Blizzard26/OAM-KNX2HovalGateway/include/knxprod.h

#pragma once


#define paramDelay(time) (uint32_t)( \
            (time & 0xC000) == 0xC000 ? (time & 0x3FFF) * 100 : \
            (time & 0xC000) == 0x0000 ? (time & 0x3FFF) * 1000 : \
            (time & 0xC000) == 0x4000 ? (time & 0x3FFF) * 60000 : \
            (time & 0xC000) == 0x8000 ? ((time & 0x3FFF) > 1000 ? 3600000 : \
                                         (time & 0x3FFF) * 3600000 ) : 0 )
                                             
#define ETS_ModuleId_NONE 0
#define ETS_ModuleId_BASE 1
#define ETS_ModuleId_UCT 2
#define ETS_ModuleId_HOV 3
#define ETS_ModuleId_LOG 4
#define MAIN_FirmwareName "KNX-Hoval Gateway"
#define MAIN_OpenKnxId 0xFF
#define MAIN_ApplicationNumber 26
#define MAIN_ApplicationVersion 4
#define MAIN_FirmwareRevision 0
#define MAIN_ApplicationEncoding iso-8859-15
#define MAIN_ParameterSize 4949
#define MAIN_MaxKoNumber 1059
#define MAIN_OrderNumber "AL-OpenKnxHovalGateway"
#define BASE_ModuleVersion 23
#define UCT_ModuleVersion 5
#define HOV_ModuleVersion 4
#define LOG_ModuleVersion 64
// Parameter with single occurrence


#define BASE_StartupDelayBase                     0      // 2 Bits, Bit 7-6
#define     BASE_StartupDelayBaseMask 0xC0
#define     BASE_StartupDelayBaseShift 6
#define BASE_StartupDelayTime                     0      // 14 Bits, Bit 13-0
#define     BASE_StartupDelayTimeMask 0x3FFF
#define     BASE_StartupDelayTimeShift 0
#define BASE_HeartbeatDelayBase                   2      // 2 Bits, Bit 7-6
#define     BASE_HeartbeatDelayBaseMask 0xC0
#define     BASE_HeartbeatDelayBaseShift 6
#define BASE_HeartbeatDelayTime                   2      // 14 Bits, Bit 13-0
#define     BASE_HeartbeatDelayTimeMask 0x3FFF
#define     BASE_HeartbeatDelayTimeShift 0
#define BASE_Timezone                             4      // 5 Bits, Bit 7-3
#define     BASE_TimezoneMask 0xF8
#define     BASE_TimezoneShift 3
#define BASE_CombinedTimeDate                     4      // 1 Bit, Bit 2
#define     BASE_CombinedTimeDateMask 0x04
#define     BASE_CombinedTimeDateShift 2
#define BASE_SummertimeAll                        4      // 2 Bits, Bit 1-0
#define     BASE_SummertimeAllMask 0x03
#define     BASE_SummertimeAllShift 0
#define BASE_SummertimeDE                         4      // 2 Bits, Bit 1-0
#define     BASE_SummertimeDEMask 0x03
#define     BASE_SummertimeDEShift 0
#define BASE_SummertimeWorld                      4      // 2 Bits, Bit 1-0
#define     BASE_SummertimeWorldMask 0x03
#define     BASE_SummertimeWorldShift 0
#define BASE_SummertimeKO                         4      // 2 Bits, Bit 1-0
#define     BASE_SummertimeKOMask 0x03
#define     BASE_SummertimeKOShift 0
#define BASE_TimezoneCustom                       5      // char*, 63 Byte
#define     BASE_TimezoneCustomLength 63
#define BASE_Latitude                            69      // float (4 Byte)
#define BASE_Longitude                           73      // float (4 Byte)
#define BASE_Diagnose                            78      // 1 Bit, Bit 7
#define     BASE_DiagnoseMask 0x80
#define     BASE_DiagnoseShift 7
#define BASE_Watchdog                            78      // 1 Bit, Bit 6
#define     BASE_WatchdogMask 0x40
#define     BASE_WatchdogShift 6
#define BASE_ReadTimeDate                        78      // 1 Bit, Bit 5
#define     BASE_ReadTimeDateMask 0x20
#define     BASE_ReadTimeDateShift 5
#define BASE_HeartbeatExtended                   78      // 1 Bit, Bit 4
#define     BASE_HeartbeatExtendedMask 0x10
#define     BASE_HeartbeatExtendedShift 4
#define BASE_InternalTime                        78      // 1 Bit, Bit 3
#define     BASE_InternalTimeMask 0x08
#define     BASE_InternalTimeShift 3
#define BASE_ManualSave                          78      // 3 Bits, Bit 2-0
#define     BASE_ManualSaveMask 0x07
#define     BASE_ManualSaveShift 0
#define BASE_PeriodicSave                        79      // 8 Bits, Bit 7-0
#define BASE_Info1LedFunc                        80      // 16 Bits, Bit 15-0
#define BASE_Info2LedFunc                        82      // 16 Bits, Bit 15-0
#define BASE_Info3LedFunc                        84      // 16 Bits, Bit 15-0
#define BASE_DefaultLedFunc                      86      // 1 Bit, Bit 7
#define     BASE_DefaultLedFuncMask 0x80
#define     BASE_DefaultLedFuncShift 7
#define BASE_Dummy                               109      // uint8_t
#define BASE_ModuleEnabled_UCT                   110      // 1 Bit, Bit 6
#define     BASE_ModuleEnabled_UCTMask 0x40
#define     BASE_ModuleEnabled_UCTShift 6
#define BASE_ModuleEnabled_HOV                   110      // 1 Bit, Bit 5
#define     BASE_ModuleEnabled_HOVMask 0x20
#define     BASE_ModuleEnabled_HOVShift 5
#define BASE_ModuleEnabled_LOG                   110      // 1 Bit, Bit 4
#define     BASE_ModuleEnabled_LOGMask 0x10
#define     BASE_ModuleEnabled_LOGShift 4

// Zeitbasis
#define ParamBASE_StartupDelayBase                    ((knx.paramByte(BASE_StartupDelayBase) & BASE_StartupDelayBaseMask) >> BASE_StartupDelayBaseShift)
// Zeit
#define ParamBASE_StartupDelayTime                    (knx.paramWord(BASE_StartupDelayTime) & BASE_StartupDelayTimeMask)
// Zeit (in Millisekunden)
#define ParamBASE_StartupDelayTimeMS                  (paramDelay(knx.paramWord(BASE_StartupDelayTime)))
// Zeitbasis
#define ParamBASE_HeartbeatDelayBase                  ((knx.paramByte(BASE_HeartbeatDelayBase) & BASE_HeartbeatDelayBaseMask) >> BASE_HeartbeatDelayBaseShift)
// Zeit
#define ParamBASE_HeartbeatDelayTime                  (knx.paramWord(BASE_HeartbeatDelayTime) & BASE_HeartbeatDelayTimeMask)
// Zeit (in Millisekunden)
#define ParamBASE_HeartbeatDelayTimeMS                (paramDelay(knx.paramWord(BASE_HeartbeatDelayTime)))
// Zeitzone
#define ParamBASE_Timezone                            ((knx.paramByte(BASE_Timezone) & BASE_TimezoneMask) >> BASE_TimezoneShift)
// Empfangen über
#define ParamBASE_CombinedTimeDate                    ((bool)(knx.paramByte(BASE_CombinedTimeDate) & BASE_CombinedTimeDateMask))
// Sommerzeit ermitteln durch
#define ParamBASE_SummertimeAll                       (knx.paramByte(BASE_SummertimeAll) & BASE_SummertimeAllMask)
// Sommerzeit ermitteln durch
#define ParamBASE_SummertimeDE                        (knx.paramByte(BASE_SummertimeDE) & BASE_SummertimeDEMask)
// Sommerzeit ermitteln durch
#define ParamBASE_SummertimeWorld                     (knx.paramByte(BASE_SummertimeWorld) & BASE_SummertimeWorldMask)
// Sommerzeit ermitteln durch
#define ParamBASE_SummertimeKO                        (knx.paramByte(BASE_SummertimeKO) & BASE_SummertimeKOMask)
// POSIX TZ-String
#define ParamBASE_TimezoneCustom                      (knx.paramData(BASE_TimezoneCustom))
#define ParamBASE_TimezoneCustomStr                   (knx.paramString(BASE_TimezoneCustom, BASE_TimezoneCustomLength))
// Breitengrad
#define ParamBASE_Latitude                            (knx.paramFloat(BASE_Latitude, Float_Enc_IEEE754Single))
// Längengrad
#define ParamBASE_Longitude                           (knx.paramFloat(BASE_Longitude, Float_Enc_IEEE754Single))
// Diagnoseobjekt anzeigen
#define ParamBASE_Diagnose                            ((bool)(knx.paramByte(BASE_Diagnose) & BASE_DiagnoseMask))
// Watchdog aktivieren
#define ParamBASE_Watchdog                            ((bool)(knx.paramByte(BASE_Watchdog) & BASE_WatchdogMask))
// Bei Neustart vom Bus lesen
#define ParamBASE_ReadTimeDate                        ((bool)(knx.paramByte(BASE_ReadTimeDate) & BASE_ReadTimeDateMask))
// Erweitertes "In Betrieb"
#define ParamBASE_HeartbeatExtended                   ((bool)(knx.paramByte(BASE_HeartbeatExtended) & BASE_HeartbeatExtendedMask))
// InternalTime
#define ParamBASE_InternalTime                        ((bool)(knx.paramByte(BASE_InternalTime) & BASE_InternalTimeMask))
// Manuelles speichern
#define ParamBASE_ManualSave                          (knx.paramByte(BASE_ManualSave) & BASE_ManualSaveMask)
// Zyklisches speichern
#define ParamBASE_PeriodicSave                        (knx.paramByte(BASE_PeriodicSave))
// Info1
#define ParamBASE_Info1LedFunc                        (knx.paramWord(BASE_Info1LedFunc))
// Info2
#define ParamBASE_Info2LedFunc                        (knx.paramWord(BASE_Info2LedFunc))
// Info3
#define ParamBASE_Info3LedFunc                        (knx.paramWord(BASE_Info3LedFunc))
// 
#define ParamBASE_DefaultLedFunc                      ((bool)(knx.paramByte(BASE_DefaultLedFunc) & BASE_DefaultLedFuncMask))
// 
#define ParamBASE_Dummy                               (knx.paramByte(BASE_Dummy))
// UCT
#define ParamBASE_ModuleEnabled_UCT                   ((bool)(knx.paramByte(BASE_ModuleEnabled_UCT) & BASE_ModuleEnabled_UCTMask))
// HOV
#define ParamBASE_ModuleEnabled_HOV                   ((bool)(knx.paramByte(BASE_ModuleEnabled_HOV) & BASE_ModuleEnabled_HOVMask))
// LOG
#define ParamBASE_ModuleEnabled_LOG                   ((bool)(knx.paramByte(BASE_ModuleEnabled_LOG) & BASE_ModuleEnabled_LOGMask))

#define BASE_KoHeartbeat 1
#define BASE_KoTime 2
#define BASE_KoDate 3
#define BASE_KoDateTime 4
#define BASE_KoIsSummertime 5
#define BASE_KoManualSave 6
#define BASE_KoDiagnose 7

// In Betrieb
#define KoBASE_Heartbeat                           (knx.getGroupObject(BASE_KoHeartbeat))
// Uhrzeit
#define KoBASE_Time                                (knx.getGroupObject(BASE_KoTime))
// Datum
#define KoBASE_Date                                (knx.getGroupObject(BASE_KoDate))
// Uhrzeit/Datum
#define KoBASE_DateTime                            (knx.getGroupObject(BASE_KoDateTime))
// Sommerzeit aktiv
#define KoBASE_IsSummertime                        (knx.getGroupObject(BASE_KoIsSummertime))
// Speichern
#define KoBASE_ManualSave                          (knx.getGroupObject(BASE_KoManualSave))
// Diagnose
#define KoBASE_Diagnose                            (knx.getGroupObject(BASE_KoDiagnose))



#define HOV_GatewayDeviceType                   114      // uint8_t
#define HOV_GatewayDeviceId                     115      // uint8_t
#define HOV_GeneralExpertMode                   116      // 1 Bit, Bit 7
#define     HOV_GeneralExpertModeMask 0x80
#define     HOV_GeneralExpertModeShift 7
#define HOV_HVDeviceType                        122      // uint8_t
#define HOV_HVDeviceId                          123      // uint8_t
#define HOV_HVSendActiveDelayBase               124      // 2 Bits, Bit 7-6
#define     HOV_HVSendActiveDelayBaseMask 0xC0
#define     HOV_HVSendActiveDelayBaseShift 6
#define HOV_HVSendActiveDelayTime               124      // 14 Bits, Bit 13-0
#define     HOV_HVSendActiveDelayTimeMask 0x3FFF
#define     HOV_HVSendActiveDelayTimeShift 0
#define HOV_HVVocSensorPresent                  126      // 1 Bit, Bit 7
#define     HOV_HVVocSensorPresentMask 0x80
#define     HOV_HVVocSensorPresentShift 7
#define HOV_GeneralRpm2Present                  126      // 1 Bit, Bit 6
#define     HOV_GeneralRpm2PresentMask 0x40
#define     HOV_GeneralRpm2PresentShift 6
#define HOV_HVPollingIntervalDelayBase          127      // 2 Bits, Bit 7-6
#define     HOV_HVPollingIntervalDelayBaseMask 0xC0
#define     HOV_HVPollingIntervalDelayBaseShift 6
#define HOV_HVPollingIntervalDelayTime          127      // 14 Bits, Bit 13-0
#define     HOV_HVPollingIntervalDelayTimeMask 0x3FFF
#define     HOV_HVPollingIntervalDelayTimeShift 0
#define HOV_HVSendEveryChange                   128      // 1 Bit, Bit 7
#define     HOV_HVSendEveryChangeMask 0x80
#define     HOV_HVSendEveryChangeShift 7
#define HOV_HVsendIntervalDelayBase             129      // 2 Bits, Bit 7-6
#define     HOV_HVsendIntervalDelayBaseMask 0xC0
#define     HOV_HVsendIntervalDelayBaseShift 6
#define HOV_HVSendIntervalDelayTime             129      // 14 Bits, Bit 13-0
#define     HOV_HVSendIntervalDelayTimeMask 0x3FFF
#define     HOV_HVSendIntervalDelayTimeShift 0
#define HOV_dummy                               138      // 1 Bit, Bit 7
#define     HOV_dummyMask 0x80
#define     HOV_dummyShift 7

// Gateway Typ (wird verwendet für Anfragen an die Lüftung; Typisch 64)
#define ParamHOV_GatewayDeviceType                   (knx.paramByte(HOV_GatewayDeviceType))
// Gateway Id (wird verwendet für Anfragen an die Lüftung; Typisch 8 oder 9)
#define ParamHOV_GatewayDeviceId                     (knx.paramByte(HOV_GatewayDeviceId))
// Expertenmodus
#define ParamHOV_GeneralExpertMode                   ((bool)(knx.paramByte(HOV_GeneralExpertMode) & HOV_GeneralExpertModeMask))
// Typ (HomeVent: 32)
#define ParamHOV_HVDeviceType                        (knx.paramByte(HOV_HVDeviceType))
// Addresse (Typisch 8)
#define ParamHOV_HVDeviceId                          (knx.paramByte(HOV_HVDeviceId))
// Zeitbasis
#define ParamHOV_HVSendActiveDelayBase               ((knx.paramByte(HOV_HVSendActiveDelayBase) & HOV_HVSendActiveDelayBaseMask) >> HOV_HVSendActiveDelayBaseShift)
// Zeit
#define ParamHOV_HVSendActiveDelayTime               (knx.paramWord(HOV_HVSendActiveDelayTime) & HOV_HVSendActiveDelayTimeMask)
// Zeit (in Millisekunden)
#define ParamHOV_HVSendActiveDelayTimeMS             (paramDelay(knx.paramWord(HOV_HVSendActiveDelayTime)))
// VOC Sensor vorhanden
#define ParamHOV_HVVocSensorPresent                  ((bool)(knx.paramByte(HOV_HVVocSensorPresent) & HOV_HVVocSensorPresentMask))
// RPM2 Present
#define ParamHOV_GeneralRpm2Present                  ((bool)(knx.paramByte(HOV_GeneralRpm2Present) & HOV_GeneralRpm2PresentMask))
// Zeitbasis
#define ParamHOV_HVPollingIntervalDelayBase          ((knx.paramByte(HOV_HVPollingIntervalDelayBase) & HOV_HVPollingIntervalDelayBaseMask) >> HOV_HVPollingIntervalDelayBaseShift)
// Zeit
#define ParamHOV_HVPollingIntervalDelayTime          (knx.paramWord(HOV_HVPollingIntervalDelayTime) & HOV_HVPollingIntervalDelayTimeMask)
// Zeit (in Millisekunden)
#define ParamHOV_HVPollingIntervalDelayTimeMS        (paramDelay(knx.paramWord(HOV_HVPollingIntervalDelayTime)))
// Jede Änderung senden
#define ParamHOV_HVSendEveryChange                   ((bool)(knx.paramByte(HOV_HVSendEveryChange) & HOV_HVSendEveryChangeMask))
// Zeitbasis
#define ParamHOV_HVsendIntervalDelayBase             ((knx.paramByte(HOV_HVsendIntervalDelayBase) & HOV_HVsendIntervalDelayBaseMask) >> HOV_HVsendIntervalDelayBaseShift)
// Zeit
#define ParamHOV_HVSendIntervalDelayTime             (knx.paramWord(HOV_HVSendIntervalDelayTime) & HOV_HVSendIntervalDelayTimeMask)
// Zeit (in Millisekunden)
#define ParamHOV_HVSendIntervalDelayTimeMS           (paramDelay(knx.paramWord(HOV_HVSendIntervalDelayTime)))
// Dummy
#define ParamHOV_dummy                               ((bool)(knx.paramByte(HOV_dummy) & HOV_dummyMask))

#define HOV_Koglobal_online 100
#define HOV_Kogeneral_diagnose 103
#define HOV_Kogeneral_maintenance_remaining 109
#define HOV_Kovent_operating_mode_standby 110
#define HOV_Kovent_operating_mode_week1 111
#define HOV_Kovent_operating_mode_week2 112
#define HOV_Kovent_operating_mode_constant 113
#define HOV_Kovent_operating_mode_economy 114
#define HOV_Kovent_operating_mode 119
#define HOV_Kovent_airqualitycontrol_standby 120
#define HOV_Kovent_airqualitycontrol_normal 121
#define HOV_Kovent_airqualitycontrol_voc 122
#define HOV_Kovent_airqualitycontrol_humidity 123
#define HOV_Kovent_airqualitycontrol_antifreeze 124
#define HOV_Kovent_airqualitycontrol_coolvent 125
#define HOV_Kovent_airqualitycontrol_error 126
#define HOV_Kovent_airqualitycontrol 129
#define HOV_Kovent_ventilation_control_status 139
#define HOV_Kovent_modulation 140
#define HOV_Kovent_normal_modulation 141
#define HOV_Kovent_economy_modulation 142
#define HOV_Kovent_party_mode 150
#define HOV_Kovent_pause_mode 151
#define HOV_Kovent_party_value 152
#define HOV_Kovent_pause_value 153
#define HOV_Kovent_humidity_setpoint 160
#define HOV_Kovent_humidity_exhaust 162
#define HOV_Kovent_temperature_outdoor 164
#define HOV_Kovent_temperature_exhaust 165
#define HOV_Kovent_voc_outdoor 167
#define HOV_Kovent_voc_exhaust 168
#define HOV_Kovent_ventilation_exhaust 170
#define HOV_Kogeneral_ventilator_outdoor_pwm 171
#define HOV_Kogeneral_ventilator_exhaust_pwm 172
#define HOV_Kogeneral_rpm_rotor1 173
#define HOV_Kogeneral_rpm_rotor2 174
#define HOV_Kogeneral_active_error 190
#define HOV_Kogeneral_active_error_1 191
#define HOV_Kogeneral_active_error_2 192
#define HOV_Kogeneral_active_error_3 193
#define HOV_Kogeneral_active_error_4 194
#define HOV_Kogeneral_active_error_5 195
#define HOV_Kogeneral_active_error_error 196
#define HOV_Kogeneral_active_error_warning 197

// Allgemein
#define KoHOV_global_online                       (knx.getGroupObject(HOV_Koglobal_online))
// Allgemein
#define KoHOV_general_diagnose                    (knx.getGroupObject(HOV_Kogeneral_diagnose))
// Allgemein
#define KoHOV_general_maintenance_remaining       (knx.getGroupObject(HOV_Kogeneral_maintenance_remaining))
// Betriebswahl Lüftung
#define KoHOV_vent_operating_mode_standby         (knx.getGroupObject(HOV_Kovent_operating_mode_standby))
// Betriebswahl Lüftung
#define KoHOV_vent_operating_mode_week1           (knx.getGroupObject(HOV_Kovent_operating_mode_week1))
// Betriebswahl Lüftung
#define KoHOV_vent_operating_mode_week2           (knx.getGroupObject(HOV_Kovent_operating_mode_week2))
// Betriebswahl Lüftung
#define KoHOV_vent_operating_mode_constant        (knx.getGroupObject(HOV_Kovent_operating_mode_constant))
// Betriebswahl Lüftung
#define KoHOV_vent_operating_mode_economy         (knx.getGroupObject(HOV_Kovent_operating_mode_economy))
// Betriebswahl Lüftung
#define KoHOV_vent_operating_mode                 (knx.getGroupObject(HOV_Kovent_operating_mode))
// Lüftungsregelung
#define KoHOV_vent_airqualitycontrol_standby      (knx.getGroupObject(HOV_Kovent_airqualitycontrol_standby))
// Lüftungsregelung
#define KoHOV_vent_airqualitycontrol_normal       (knx.getGroupObject(HOV_Kovent_airqualitycontrol_normal))
// Lüftungsregelung
#define KoHOV_vent_airqualitycontrol_voc          (knx.getGroupObject(HOV_Kovent_airqualitycontrol_voc))
// Lüftungsregelung
#define KoHOV_vent_airqualitycontrol_humidity     (knx.getGroupObject(HOV_Kovent_airqualitycontrol_humidity))
// Lüftungsregelung
#define KoHOV_vent_airqualitycontrol_antifreeze   (knx.getGroupObject(HOV_Kovent_airqualitycontrol_antifreeze))
// Lüftungsregelung
#define KoHOV_vent_airqualitycontrol_coolvent     (knx.getGroupObject(HOV_Kovent_airqualitycontrol_coolvent))
// Lüftungsregelung
#define KoHOV_vent_airqualitycontrol_error        (knx.getGroupObject(HOV_Kovent_airqualitycontrol_error))
// Lüftungsregelung
#define KoHOV_vent_airqualitycontrol              (knx.getGroupObject(HOV_Kovent_airqualitycontrol))
// Lüftung
#define KoHOV_vent_ventilation_control_status     (knx.getGroupObject(HOV_Kovent_ventilation_control_status))
// Lüftungsmodulation
#define KoHOV_vent_modulation                     (knx.getGroupObject(HOV_Kovent_modulation))
// Lüftungsmodulation
#define KoHOV_vent_normal_modulation              (knx.getGroupObject(HOV_Kovent_normal_modulation))
// Lüftungsmodulation
#define KoHOV_vent_economy_modulation             (knx.getGroupObject(HOV_Kovent_economy_modulation))
// Party/Pause
#define KoHOV_vent_party_mode                     (knx.getGroupObject(HOV_Kovent_party_mode))
// Party/Pause
#define KoHOV_vent_pause_mode                     (knx.getGroupObject(HOV_Kovent_pause_mode))
// Party/Pause
#define KoHOV_vent_party_value                    (knx.getGroupObject(HOV_Kovent_party_value))
// Party/Pause
#define KoHOV_vent_pause_value                    (knx.getGroupObject(HOV_Kovent_pause_value))
// Luftfeuchtigkeit
#define KoHOV_vent_humidity_setpoint              (knx.getGroupObject(HOV_Kovent_humidity_setpoint))
// Luftfeuchtigkeit
#define KoHOV_vent_humidity_exhaust               (knx.getGroupObject(HOV_Kovent_humidity_exhaust))
// Temperatur
#define KoHOV_vent_temperature_outdoor            (knx.getGroupObject(HOV_Kovent_temperature_outdoor))
// Temperatur
#define KoHOV_vent_temperature_exhaust            (knx.getGroupObject(HOV_Kovent_temperature_exhaust))
// VOC
#define KoHOV_vent_voc_outdoor                    (knx.getGroupObject(HOV_Kovent_voc_outdoor))
// VOC
#define KoHOV_vent_voc_exhaust                    (knx.getGroupObject(HOV_Kovent_voc_exhaust))
// Ventilator
#define KoHOV_vent_ventilation_exhaust            (knx.getGroupObject(HOV_Kovent_ventilation_exhaust))
// Ventilator
#define KoHOV_general_ventilator_outdoor_pwm      (knx.getGroupObject(HOV_Kogeneral_ventilator_outdoor_pwm))
// Ventilator 
#define KoHOV_general_ventilator_exhaust_pwm      (knx.getGroupObject(HOV_Kogeneral_ventilator_exhaust_pwm))
// Ventilator
#define KoHOV_general_rpm_rotor1                  (knx.getGroupObject(HOV_Kogeneral_rpm_rotor1))
// Ventilator
#define KoHOV_general_rpm_rotor2                  (knx.getGroupObject(HOV_Kogeneral_rpm_rotor2))
// Allgemein
#define KoHOV_general_active_error                (knx.getGroupObject(HOV_Kogeneral_active_error))
// Allgemein
#define KoHOV_general_active_error_1              (knx.getGroupObject(HOV_Kogeneral_active_error_1))
// Allgemein
#define KoHOV_general_active_error_2              (knx.getGroupObject(HOV_Kogeneral_active_error_2))
// Allgemein
#define KoHOV_general_active_error_3              (knx.getGroupObject(HOV_Kogeneral_active_error_3))
// Allgemein
#define KoHOV_general_active_error_4              (knx.getGroupObject(HOV_Kogeneral_active_error_4))
// Allgemein
#define KoHOV_general_active_error_5              (knx.getGroupObject(HOV_Kogeneral_active_error_5))
// Allgemein
#define KoHOV_general_active_error_error          (knx.getGroupObject(HOV_Kogeneral_active_error_error))
// Allgemein
#define KoHOV_general_active_error_warning        (knx.getGroupObject(HOV_Kogeneral_active_error_warning))

#define LOG_VisibleChannels                     202      // uint8_t
#define LOG_VacationKo                          203      // 1 Bit, Bit 7
#define     LOG_VacationKoMask 0x80
#define     LOG_VacationKoShift 7
#define LOG_HolidayKo                           203      // 1 Bit, Bit 6
#define     LOG_HolidayKoMask 0x40
#define     LOG_HolidayKoShift 6
#define LOG_VacationRead                        203      // 1 Bit, Bit 5
#define     LOG_VacationReadMask 0x20
#define     LOG_VacationReadShift 5
#define LOG_HolidaySend                         203      // 1 Bit, Bit 4
#define     LOG_HolidaySendMask 0x10
#define     LOG_HolidaySendShift 4
#define LOG_Neujahr                             204      // 1 Bit, Bit 7
#define     LOG_NeujahrMask 0x80
#define     LOG_NeujahrShift 7
#define LOG_DreiKoenige                         204      // 1 Bit, Bit 6
#define     LOG_DreiKoenigeMask 0x40
#define     LOG_DreiKoenigeShift 6
#define LOG_Weiberfastnacht                     204      // 1 Bit, Bit 5
#define     LOG_WeiberfastnachtMask 0x20
#define     LOG_WeiberfastnachtShift 5
#define LOG_Rosenmontag                         204      // 1 Bit, Bit 4
#define     LOG_RosenmontagMask 0x10
#define     LOG_RosenmontagShift 4
#define LOG_Fastnachtsdienstag                  204      // 1 Bit, Bit 3
#define     LOG_FastnachtsdienstagMask 0x08
#define     LOG_FastnachtsdienstagShift 3
#define LOG_Aschermittwoch                      204      // 1 Bit, Bit 2
#define     LOG_AschermittwochMask 0x04
#define     LOG_AschermittwochShift 2
#define LOG_Frauentag                           204      // 1 Bit, Bit 1
#define     LOG_FrauentagMask 0x02
#define     LOG_FrauentagShift 1
#define LOG_Gruendonnerstag                     204      // 1 Bit, Bit 0
#define     LOG_GruendonnerstagMask 0x01
#define     LOG_GruendonnerstagShift 0
#define LOG_Karfreitag                          205      // 1 Bit, Bit 7
#define     LOG_KarfreitagMask 0x80
#define     LOG_KarfreitagShift 7
#define LOG_Ostersonntag                        205      // 1 Bit, Bit 6
#define     LOG_OstersonntagMask 0x40
#define     LOG_OstersonntagShift 6
#define LOG_Ostermontag                         205      // 1 Bit, Bit 5
#define     LOG_OstermontagMask 0x20
#define     LOG_OstermontagShift 5
#define LOG_TagDerArbeit                        205      // 1 Bit, Bit 4
#define     LOG_TagDerArbeitMask 0x10
#define     LOG_TagDerArbeitShift 4
#define LOG_Himmelfahrt                         205      // 1 Bit, Bit 3
#define     LOG_HimmelfahrtMask 0x08
#define     LOG_HimmelfahrtShift 3
#define LOG_Pfingstsonntag                      205      // 1 Bit, Bit 2
#define     LOG_PfingstsonntagMask 0x04
#define     LOG_PfingstsonntagShift 2
#define LOG_Pfingstmontag                       205      // 1 Bit, Bit 1
#define     LOG_PfingstmontagMask 0x02
#define     LOG_PfingstmontagShift 1
#define LOG_Fronleichnam                        205      // 1 Bit, Bit 0
#define     LOG_FronleichnamMask 0x01
#define     LOG_FronleichnamShift 0
#define LOG_Friedensfest                        206      // 1 Bit, Bit 7
#define     LOG_FriedensfestMask 0x80
#define     LOG_FriedensfestShift 7
#define LOG_MariaHimmelfahrt                    206      // 1 Bit, Bit 6
#define     LOG_MariaHimmelfahrtMask 0x40
#define     LOG_MariaHimmelfahrtShift 6
#define LOG_DeutscheEinheit                     206      // 1 Bit, Bit 5
#define     LOG_DeutscheEinheitMask 0x20
#define     LOG_DeutscheEinheitShift 5
#define LOG_Reformationstag                     206      // 1 Bit, Bit 4
#define     LOG_ReformationstagMask 0x10
#define     LOG_ReformationstagShift 4
#define LOG_Allerheiligen                       206      // 1 Bit, Bit 3
#define     LOG_AllerheiligenMask 0x08
#define     LOG_AllerheiligenShift 3
#define LOG_BussBettag                          206      // 1 Bit, Bit 2
#define     LOG_BussBettagMask 0x04
#define     LOG_BussBettagShift 2
#define LOG_Advent1                             206      // 1 Bit, Bit 1
#define     LOG_Advent1Mask 0x02
#define     LOG_Advent1Shift 1
#define LOG_Advent2                             206      // 1 Bit, Bit 0
#define     LOG_Advent2Mask 0x01
#define     LOG_Advent2Shift 0
#define LOG_Advent3                             207      // 1 Bit, Bit 7
#define     LOG_Advent3Mask 0x80
#define     LOG_Advent3Shift 7
#define LOG_Advent4                             207      // 1 Bit, Bit 6
#define     LOG_Advent4Mask 0x40
#define     LOG_Advent4Shift 6
#define LOG_Heiligabend                         207      // 1 Bit, Bit 5
#define     LOG_HeiligabendMask 0x20
#define     LOG_HeiligabendShift 5
#define LOG_Weihnachtstag1                      207      // 1 Bit, Bit 4
#define     LOG_Weihnachtstag1Mask 0x10
#define     LOG_Weihnachtstag1Shift 4
#define LOG_Weihnachtstag2                      207      // 1 Bit, Bit 3
#define     LOG_Weihnachtstag2Mask 0x08
#define     LOG_Weihnachtstag2Shift 3
#define LOG_Silvester                           207      // 1 Bit, Bit 2
#define     LOG_SilvesterMask 0x04
#define     LOG_SilvesterShift 2
#define LOG_Nationalfeiertag                    207      // 1 Bit, Bit 1
#define     LOG_NationalfeiertagMask 0x02
#define     LOG_NationalfeiertagShift 1
#define LOG_MariaEmpfaengnis                    207      // 1 Bit, Bit 0
#define     LOG_MariaEmpfaengnisMask 0x01
#define     LOG_MariaEmpfaengnisShift 0
#define LOG_NationalfeiertagSchweiz             208      // 1 Bit, Bit 7
#define     LOG_NationalfeiertagSchweizMask 0x80
#define     LOG_NationalfeiertagSchweizShift 7
#define LOG_Totensonntag                        208      // 1 Bit, Bit 6
#define     LOG_TotensonntagMask 0x40
#define     LOG_TotensonntagShift 6
#define LOG_Weltkindertag                       208      // 1 Bit, Bit 5
#define     LOG_WeltkindertagMask 0x20
#define     LOG_WeltkindertagShift 5
#define LOG_UserFormula1                        209      // char*, 99 Byte
#define     LOG_UserFormula1Length 99
#define LOG_UserFormula1Active                  308      // 1 Bit, Bit 7
#define     LOG_UserFormula1ActiveMask 0x80
#define     LOG_UserFormula1ActiveShift 7
#define LOG_UserFormula2                        309      // char*, 99 Byte
#define     LOG_UserFormula2Length 99
#define LOG_UserFormula2Active                  408      // 1 Bit, Bit 7
#define     LOG_UserFormula2ActiveMask 0x80
#define     LOG_UserFormula2ActiveShift 7
#define LOG_UserFormula3                        409      // char*, 99 Byte
#define     LOG_UserFormula3Length 99
#define LOG_UserFormula3Active                  508      // 1 Bit, Bit 7
#define     LOG_UserFormula3ActiveMask 0x80
#define     LOG_UserFormula3ActiveShift 7
#define LOG_UserFormula4                        509      // char*, 99 Byte
#define     LOG_UserFormula4Length 99
#define LOG_UserFormula4Active                  608      // 1 Bit, Bit 7
#define     LOG_UserFormula4ActiveMask 0x80
#define     LOG_UserFormula4ActiveShift 7
#define LOG_UserFormula5                        609      // char*, 99 Byte
#define     LOG_UserFormula5Length 99
#define LOG_UserFormula5Active                  708      // 1 Bit, Bit 7
#define     LOG_UserFormula5ActiveMask 0x80
#define     LOG_UserFormula5ActiveShift 7
#define LOG_UserFormula6                        709      // char*, 99 Byte
#define     LOG_UserFormula6Length 99
#define LOG_UserFormula6Active                  808      // 1 Bit, Bit 7
#define     LOG_UserFormula6ActiveMask 0x80
#define     LOG_UserFormula6ActiveShift 7
#define LOG_UserFormula7                        809      // char*, 99 Byte
#define     LOG_UserFormula7Length 99
#define LOG_UserFormula7Active                  908      // 1 Bit, Bit 7
#define     LOG_UserFormula7ActiveMask 0x80
#define     LOG_UserFormula7ActiveShift 7
#define LOG_UserFormula8                        909      // char*, 99 Byte
#define     LOG_UserFormula8Length 99
#define LOG_UserFormula8Active                  1008      // 1 Bit, Bit 7
#define     LOG_UserFormula8ActiveMask 0x80
#define     LOG_UserFormula8ActiveShift 7
#define LOG_UserFormula9                        1009      // char*, 99 Byte
#define     LOG_UserFormula9Length 99
#define LOG_UserFormula9Active                  1108      // 1 Bit, Bit 7
#define     LOG_UserFormula9ActiveMask 0x80
#define     LOG_UserFormula9ActiveShift 7
#define LOG_UserFormula10                       1109      // char*, 99 Byte
#define     LOG_UserFormula10Length 99
#define LOG_UserFormula10Active                 1208      // 1 Bit, Bit 7
#define     LOG_UserFormula10ActiveMask 0x80
#define     LOG_UserFormula10ActiveShift 7
#define LOG_UserFormula11                       1209      // char*, 99 Byte
#define     LOG_UserFormula11Length 99
#define LOG_UserFormula11Active                 1308      // 1 Bit, Bit 7
#define     LOG_UserFormula11ActiveMask 0x80
#define     LOG_UserFormula11ActiveShift 7
#define LOG_UserFormula12                       1309      // char*, 99 Byte
#define     LOG_UserFormula12Length 99
#define LOG_UserFormula12Active                 1408      // 1 Bit, Bit 7
#define     LOG_UserFormula12ActiveMask 0x80
#define     LOG_UserFormula12ActiveShift 7
#define LOG_UserFormula13                       1409      // char*, 99 Byte
#define     LOG_UserFormula13Length 99
#define LOG_UserFormula13Active                 1508      // 1 Bit, Bit 7
#define     LOG_UserFormula13ActiveMask 0x80
#define     LOG_UserFormula13ActiveShift 7
#define LOG_UserFormula14                       1509      // char*, 99 Byte
#define     LOG_UserFormula14Length 99
#define LOG_UserFormula14Active                 1608      // 1 Bit, Bit 7
#define     LOG_UserFormula14ActiveMask 0x80
#define     LOG_UserFormula14ActiveShift 7
#define LOG_UserFormula15                       1609      // char*, 99 Byte
#define     LOG_UserFormula15Length 99
#define LOG_UserFormula15Active                 1708      // 1 Bit, Bit 7
#define     LOG_UserFormula15ActiveMask 0x80
#define     LOG_UserFormula15ActiveShift 7
#define LOG_UserFormula16                       1709      // char*, 99 Byte
#define     LOG_UserFormula16Length 99
#define LOG_UserFormula16Active                 1808      // 1 Bit, Bit 7
#define     LOG_UserFormula16ActiveMask 0x80
#define     LOG_UserFormula16ActiveShift 7
#define LOG_UserFormula17                       1809      // char*, 99 Byte
#define     LOG_UserFormula17Length 99
#define LOG_UserFormula17Active                 1908      // 1 Bit, Bit 7
#define     LOG_UserFormula17ActiveMask 0x80
#define     LOG_UserFormula17ActiveShift 7
#define LOG_UserFormula18                       1909      // char*, 99 Byte
#define     LOG_UserFormula18Length 99
#define LOG_UserFormula18Active                 2008      // 1 Bit, Bit 7
#define     LOG_UserFormula18ActiveMask 0x80
#define     LOG_UserFormula18ActiveShift 7
#define LOG_UserFormula19                       2009      // char*, 99 Byte
#define     LOG_UserFormula19Length 99
#define LOG_UserFormula19Active                 2108      // 1 Bit, Bit 7
#define     LOG_UserFormula19ActiveMask 0x80
#define     LOG_UserFormula19ActiveShift 7
#define LOG_UserFormula20                       2109      // char*, 99 Byte
#define     LOG_UserFormula20Length 99
#define LOG_UserFormula20Active                 2208      // 1 Bit, Bit 7
#define     LOG_UserFormula20ActiveMask 0x80
#define     LOG_UserFormula20ActiveShift 7
#define LOG_UserFormula21                       2209      // char*, 99 Byte
#define     LOG_UserFormula21Length 99
#define LOG_UserFormula21Active                 2308      // 1 Bit, Bit 7
#define     LOG_UserFormula21ActiveMask 0x80
#define     LOG_UserFormula21ActiveShift 7
#define LOG_UserFormula22                       2309      // char*, 99 Byte
#define     LOG_UserFormula22Length 99
#define LOG_UserFormula22Active                 2408      // 1 Bit, Bit 7
#define     LOG_UserFormula22ActiveMask 0x80
#define     LOG_UserFormula22ActiveShift 7
#define LOG_UserFormula23                       2409      // char*, 99 Byte
#define     LOG_UserFormula23Length 99
#define LOG_UserFormula23Active                 2508      // 1 Bit, Bit 7
#define     LOG_UserFormula23ActiveMask 0x80
#define     LOG_UserFormula23ActiveShift 7
#define LOG_UserFormula24                       2509      // char*, 99 Byte
#define     LOG_UserFormula24Length 99
#define LOG_UserFormula24Active                 2608      // 1 Bit, Bit 7
#define     LOG_UserFormula24ActiveMask 0x80
#define     LOG_UserFormula24ActiveShift 7
#define LOG_UserFormula25                       2609      // char*, 99 Byte
#define     LOG_UserFormula25Length 99
#define LOG_UserFormula25Active                 2708      // 1 Bit, Bit 7
#define     LOG_UserFormula25ActiveMask 0x80
#define     LOG_UserFormula25ActiveShift 7
#define LOG_UserFormula26                       2709      // char*, 99 Byte
#define     LOG_UserFormula26Length 99
#define LOG_UserFormula26Active                 2808      // 1 Bit, Bit 7
#define     LOG_UserFormula26ActiveMask 0x80
#define     LOG_UserFormula26ActiveShift 7
#define LOG_UserFormula27                       2809      // char*, 99 Byte
#define     LOG_UserFormula27Length 99
#define LOG_UserFormula27Active                 2908      // 1 Bit, Bit 7
#define     LOG_UserFormula27ActiveMask 0x80
#define     LOG_UserFormula27ActiveShift 7
#define LOG_UserFormula28                       2909      // char*, 99 Byte
#define     LOG_UserFormula28Length 99
#define LOG_UserFormula28Active                 3008      // 1 Bit, Bit 7
#define     LOG_UserFormula28ActiveMask 0x80
#define     LOG_UserFormula28ActiveShift 7
#define LOG_UserFormula29                       3009      // char*, 99 Byte
#define     LOG_UserFormula29Length 99
#define LOG_UserFormula29Active                 3108      // 1 Bit, Bit 7
#define     LOG_UserFormula29ActiveMask 0x80
#define     LOG_UserFormula29ActiveShift 7
#define LOG_UserFormula30                       3109      // char*, 99 Byte
#define     LOG_UserFormula30Length 99
#define LOG_UserFormula30Active                 3208      // 1 Bit, Bit 7
#define     LOG_UserFormula30ActiveMask 0x80
#define     LOG_UserFormula30ActiveShift 7

// Verfügbare Kanäle
#define ParamLOG_VisibleChannels                     (knx.paramByte(LOG_VisibleChannels))
// Urlaubsbehandlung aktivieren?
#define ParamLOG_VacationKo                          ((bool)(knx.paramByte(LOG_VacationKo) & LOG_VacationKoMask))
// Feiertage auf dem Bus verfügbar machen?
#define ParamLOG_HolidayKo                           ((bool)(knx.paramByte(LOG_HolidayKo) & LOG_HolidayKoMask))
// Nach Neustart Urlaubsinfo lesen?
#define ParamLOG_VacationRead                        ((bool)(knx.paramByte(LOG_VacationRead) & LOG_VacationReadMask))
// Nach Neuberechnung Feiertagsinfo senden?
#define ParamLOG_HolidaySend                         ((bool)(knx.paramByte(LOG_HolidaySend) & LOG_HolidaySendMask))
// 1. Neujahr
#define ParamLOG_Neujahr                             ((bool)(knx.paramByte(LOG_Neujahr) & LOG_NeujahrMask))
// 2. Heilige Drei Könige
#define ParamLOG_DreiKoenige                         ((bool)(knx.paramByte(LOG_DreiKoenige) & LOG_DreiKoenigeMask))
// 3. Weiberfastnacht
#define ParamLOG_Weiberfastnacht                     ((bool)(knx.paramByte(LOG_Weiberfastnacht) & LOG_WeiberfastnachtMask))
// 4. Rosenmontag
#define ParamLOG_Rosenmontag                         ((bool)(knx.paramByte(LOG_Rosenmontag) & LOG_RosenmontagMask))
// 5. Fastnachtsdienstag
#define ParamLOG_Fastnachtsdienstag                  ((bool)(knx.paramByte(LOG_Fastnachtsdienstag) & LOG_FastnachtsdienstagMask))
// 6. Aschermittwoch
#define ParamLOG_Aschermittwoch                      ((bool)(knx.paramByte(LOG_Aschermittwoch) & LOG_AschermittwochMask))
// 7. Frauentag
#define ParamLOG_Frauentag                           ((bool)(knx.paramByte(LOG_Frauentag) & LOG_FrauentagMask))
// 8. Gründonnerstag
#define ParamLOG_Gruendonnerstag                     ((bool)(knx.paramByte(LOG_Gruendonnerstag) & LOG_GruendonnerstagMask))
// 9. Karfreitag
#define ParamLOG_Karfreitag                          ((bool)(knx.paramByte(LOG_Karfreitag) & LOG_KarfreitagMask))
// 10. Ostersonntag
#define ParamLOG_Ostersonntag                        ((bool)(knx.paramByte(LOG_Ostersonntag) & LOG_OstersonntagMask))
// 11. Ostermontag
#define ParamLOG_Ostermontag                         ((bool)(knx.paramByte(LOG_Ostermontag) & LOG_OstermontagMask))
// 12. Tag der Arbeit
#define ParamLOG_TagDerArbeit                        ((bool)(knx.paramByte(LOG_TagDerArbeit) & LOG_TagDerArbeitMask))
// 13. Christi Himmelfahrt
#define ParamLOG_Himmelfahrt                         ((bool)(knx.paramByte(LOG_Himmelfahrt) & LOG_HimmelfahrtMask))
// 14. Pfingstsonntag
#define ParamLOG_Pfingstsonntag                      ((bool)(knx.paramByte(LOG_Pfingstsonntag) & LOG_PfingstsonntagMask))
// 15. Pfingstmontag
#define ParamLOG_Pfingstmontag                       ((bool)(knx.paramByte(LOG_Pfingstmontag) & LOG_PfingstmontagMask))
// 16. Fronleichnam
#define ParamLOG_Fronleichnam                        ((bool)(knx.paramByte(LOG_Fronleichnam) & LOG_FronleichnamMask))
// 17. Hohes Friedensfest
#define ParamLOG_Friedensfest                        ((bool)(knx.paramByte(LOG_Friedensfest) & LOG_FriedensfestMask))
// 18. Mariä Himmelfahrt
#define ParamLOG_MariaHimmelfahrt                    ((bool)(knx.paramByte(LOG_MariaHimmelfahrt) & LOG_MariaHimmelfahrtMask))
// 19. Tag der Deutschen Einheit
#define ParamLOG_DeutscheEinheit                     ((bool)(knx.paramByte(LOG_DeutscheEinheit) & LOG_DeutscheEinheitMask))
// 20. Reformationstag
#define ParamLOG_Reformationstag                     ((bool)(knx.paramByte(LOG_Reformationstag) & LOG_ReformationstagMask))
// 21. Allerheiligen
#define ParamLOG_Allerheiligen                       ((bool)(knx.paramByte(LOG_Allerheiligen) & LOG_AllerheiligenMask))
// 22. Buß- und Bettag
#define ParamLOG_BussBettag                          ((bool)(knx.paramByte(LOG_BussBettag) & LOG_BussBettagMask))
// 23. Erster Advent
#define ParamLOG_Advent1                             ((bool)(knx.paramByte(LOG_Advent1) & LOG_Advent1Mask))
// 24. Zweiter Advent
#define ParamLOG_Advent2                             ((bool)(knx.paramByte(LOG_Advent2) & LOG_Advent2Mask))
// 25. Dritter Advent
#define ParamLOG_Advent3                             ((bool)(knx.paramByte(LOG_Advent3) & LOG_Advent3Mask))
// 26. Vierter Advent
#define ParamLOG_Advent4                             ((bool)(knx.paramByte(LOG_Advent4) & LOG_Advent4Mask))
// 27. Heiligabend
#define ParamLOG_Heiligabend                         ((bool)(knx.paramByte(LOG_Heiligabend) & LOG_HeiligabendMask))
// 28. Erster Weihnachtstag
#define ParamLOG_Weihnachtstag1                      ((bool)(knx.paramByte(LOG_Weihnachtstag1) & LOG_Weihnachtstag1Mask))
// 29. Zweiter Weihnachtstag
#define ParamLOG_Weihnachtstag2                      ((bool)(knx.paramByte(LOG_Weihnachtstag2) & LOG_Weihnachtstag2Mask))
// 30. Silvester
#define ParamLOG_Silvester                           ((bool)(knx.paramByte(LOG_Silvester) & LOG_SilvesterMask))
// 31. Nationalfeiertag (AT)
#define ParamLOG_Nationalfeiertag                    ((bool)(knx.paramByte(LOG_Nationalfeiertag) & LOG_NationalfeiertagMask))
// 32. Maria Empfängnis (AT)
#define ParamLOG_MariaEmpfaengnis                    ((bool)(knx.paramByte(LOG_MariaEmpfaengnis) & LOG_MariaEmpfaengnisMask))
// 33. Nationalfeiertag (CH)
#define ParamLOG_NationalfeiertagSchweiz             ((bool)(knx.paramByte(LOG_NationalfeiertagSchweiz) & LOG_NationalfeiertagSchweizMask))
// 34. Totensonntag
#define ParamLOG_Totensonntag                        ((bool)(knx.paramByte(LOG_Totensonntag) & LOG_TotensonntagMask))
// 35. Weltkindertag
#define ParamLOG_Weltkindertag                       ((bool)(knx.paramByte(LOG_Weltkindertag) & LOG_WeltkindertagMask))
// Formeldefinition
#define ParamLOG_UserFormula1                        (knx.paramData(LOG_UserFormula1))
#define ParamLOG_UserFormula1Str                     (knx.paramString(LOG_UserFormula1, LOG_UserFormula1Length))
// Benutzerformel 1 aktiv
#define ParamLOG_UserFormula1Active                  ((bool)(knx.paramByte(LOG_UserFormula1Active) & LOG_UserFormula1ActiveMask))
// Formeldefinition
#define ParamLOG_UserFormula2                        (knx.paramData(LOG_UserFormula2))
#define ParamLOG_UserFormula2Str                     (knx.paramString(LOG_UserFormula2, LOG_UserFormula2Length))
// Benutzerformel 2 aktiv
#define ParamLOG_UserFormula2Active                  ((bool)(knx.paramByte(LOG_UserFormula2Active) & LOG_UserFormula2ActiveMask))
// Formeldefinition
#define ParamLOG_UserFormula3                        (knx.paramData(LOG_UserFormula3))
#define ParamLOG_UserFormula3Str                     (knx.paramString(LOG_UserFormula3, LOG_UserFormula3Length))
// Benutzerformel 3 aktiv
#define ParamLOG_UserFormula3Active                  ((bool)(knx.paramByte(LOG_UserFormula3Active) & LOG_UserFormula3ActiveMask))
// Formeldefinition
#define ParamLOG_UserFormula4                        (knx.paramData(LOG_UserFormula4))
#define ParamLOG_UserFormula4Str                     (knx.paramString(LOG_UserFormula4, LOG_UserFormula4Length))
// Benutzerformel 4 aktiv
#define ParamLOG_UserFormula4Active                  ((bool)(knx.paramByte(LOG_UserFormula4Active) & LOG_UserFormula4ActiveMask))
// Formeldefinition
#define ParamLOG_UserFormula5                        (knx.paramData(LOG_UserFormula5))
#define ParamLOG_UserFormula5Str                     (knx.paramString(LOG_UserFormula5, LOG_UserFormula5Length))
// Benutzerformel 5 aktiv
#define ParamLOG_UserFormula5Active                  ((bool)(knx.paramByte(LOG_UserFormula5Active) & LOG_UserFormula5ActiveMask))
// Formeldefinition
#define ParamLOG_UserFormula6                        (knx.paramData(LOG_UserFormula6))
#define ParamLOG_UserFormula6Str                     (knx.paramString(LOG_UserFormula6, LOG_UserFormula6Length))
// Benutzerformel 6 aktiv
#define ParamLOG_UserFormula6Active                  ((bool)(knx.paramByte(LOG_UserFormula6Active) & LOG_UserFormula6ActiveMask))
// Formeldefinition
#define ParamLOG_UserFormula7                        (knx.paramData(LOG_UserFormula7))
#define ParamLOG_UserFormula7Str                     (knx.paramString(LOG_UserFormula7, LOG_UserFormula7Length))
// Benutzerformel 7 aktiv
#define ParamLOG_UserFormula7Active                  ((bool)(knx.paramByte(LOG_UserFormula7Active) & LOG_UserFormula7ActiveMask))
// Formeldefinition
#define ParamLOG_UserFormula8                        (knx.paramData(LOG_UserFormula8))
#define ParamLOG_UserFormula8Str                     (knx.paramString(LOG_UserFormula8, LOG_UserFormula8Length))
// Benutzerformel 8 aktiv
#define ParamLOG_UserFormula8Active                  ((bool)(knx.paramByte(LOG_UserFormula8Active) & LOG_UserFormula8ActiveMask))
// Formeldefinition
#define ParamLOG_UserFormula9                        (knx.paramData(LOG_UserFormula9))
#define ParamLOG_UserFormula9Str                     (knx.paramString(LOG_UserFormula9, LOG_UserFormula9Length))
// Benutzerformel 9 aktiv
#define ParamLOG_UserFormula9Active                  ((bool)(knx.paramByte(LOG_UserFormula9Active) & LOG_UserFormula9ActiveMask))
// Formeldefinition
#define ParamLOG_UserFormula10                       (knx.paramData(LOG_UserFormula10))
#define ParamLOG_UserFormula10Str                    (knx.paramString(LOG_UserFormula10, LOG_UserFormula10Length))
// Benutzerformel 10 aktiv
#define ParamLOG_UserFormula10Active                 ((bool)(knx.paramByte(LOG_UserFormula10Active) & LOG_UserFormula10ActiveMask))
// Formeldefinition
#define ParamLOG_UserFormula11                       (knx.paramData(LOG_UserFormula11))
#define ParamLOG_UserFormula11Str                    (knx.paramString(LOG_UserFormula11, LOG_UserFormula11Length))
// Benutzerformel 11 aktiv
#define ParamLOG_UserFormula11Active                 ((bool)(knx.paramByte(LOG_UserFormula11Active) & LOG_UserFormula11ActiveMask))
// Formeldefinition
#define ParamLOG_UserFormula12                       (knx.paramData(LOG_UserFormula12))
#define ParamLOG_UserFormula12Str                    (knx.paramString(LOG_UserFormula12, LOG_UserFormula12Length))
// Benutzerformel 12 aktiv
#define ParamLOG_UserFormula12Active                 ((bool)(knx.paramByte(LOG_UserFormula12Active) & LOG_UserFormula12ActiveMask))
// Formeldefinition
#define ParamLOG_UserFormula13                       (knx.paramData(LOG_UserFormula13))
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
#define ParamLOG_UserFormula24Str                    (knx.paramString(LOG_UserFormula24, LOG_UserFormula24Length))
// Benutzerformel 24 aktiv
#define ParamLOG_UserFormula24Active                 ((bool)(knx.paramByte(LOG_UserFormula24Active) & LOG_UserFormula24ActiveMask))
// Formeldefinition
#define ParamLOG_UserFormula25                       (knx.paramData(LOG_UserFormula25))
#define ParamLOG_UserFormula25Str                    (knx.paramString(LOG_UserFormula25, LOG_UserFormula25Length))
// Benutzerformel 25 aktiv
#define ParamLOG_UserFormula25Active                 ((bool)(knx.paramByte(LOG_UserFormula25Active) & LOG_UserFormula25ActiveMask))
// Formeldefinition
#define ParamLOG_UserFormula26                       (knx.paramData(LOG_UserFormula26))
#define ParamLOG_UserFormula26Str                    (knx.paramString(LOG_UserFormula26, LOG_UserFormula26Length))
// Benutzerformel 26 aktiv
#define ParamLOG_UserFormula26Active                 ((bool)(knx.paramByte(LOG_UserFormula26Active) & LOG_UserFormula26ActiveMask))
// Formeldefinition
#define ParamLOG_UserFormula27                       (knx.paramData(LOG_UserFormula27))
#define ParamLOG_UserFormula27Str                    (knx.paramString(LOG_UserFormula27, LOG_UserFormula27Length))
// Benutzerformel 27 aktiv
#define ParamLOG_UserFormula27Active                 ((bool)(knx.paramByte(LOG_UserFormula27Active) & LOG_UserFormula27ActiveMask))
// Formeldefinition
#define ParamLOG_UserFormula28                       (knx.paramData(LOG_UserFormula28))
#define ParamLOG_UserFormula28Str                    (knx.paramString(LOG_UserFormula28, LOG_UserFormula28Length))
// Benutzerformel 28 aktiv
#define ParamLOG_UserFormula28Active                 ((bool)(knx.paramByte(LOG_UserFormula28Active) & LOG_UserFormula28ActiveMask))
// Formeldefinition
#define ParamLOG_UserFormula29                       (knx.paramData(LOG_UserFormula29))
#define ParamLOG_UserFormula29Str                    (knx.paramString(LOG_UserFormula29, LOG_UserFormula29Length))
// Benutzerformel 29 aktiv
#define ParamLOG_UserFormula29Active                 ((bool)(knx.paramByte(LOG_UserFormula29Active) & LOG_UserFormula29ActiveMask))
// Formeldefinition
#define ParamLOG_UserFormula30                       (knx.paramData(LOG_UserFormula30))
#define ParamLOG_UserFormula30Str                    (knx.paramString(LOG_UserFormula30, LOG_UserFormula30Length))
// Benutzerformel 30 aktiv
#define ParamLOG_UserFormula30Active                 ((bool)(knx.paramByte(LOG_UserFormula30Active) & LOG_UserFormula30ActiveMask))

#define LOG_KoVacation 15
#define LOG_KoHoliday1 16
#define LOG_KoHoliday2 17

// Urlaub
#define KoLOG_Vacation                            (knx.getGroupObject(LOG_KoVacation))
// Welcher Feiertag ist heute?
#define KoLOG_Holiday1                            (knx.getGroupObject(LOG_KoHoliday1))
// Welcher Feiertag ist morgen?
#define KoLOG_Holiday2                            (knx.getGroupObject(LOG_KoHoliday2))

#define LOG_ChannelCount 20

// Parameter per channel
#define LOG_ParamBlockOffset 3209
#define LOG_ParamBlockSize 87
#define LOG_ParamCalcIndex(index) (index + LOG_ParamBlockOffset + _channelIndex * LOG_ParamBlockSize)

#define LOG_fChannelDelayBase                    0      // 2 Bits, Bit 7-6
#define     LOG_fChannelDelayBaseMask 0xC0
#define     LOG_fChannelDelayBaseShift 6
#define LOG_fChannelDelayTime                    0      // 14 Bits, Bit 13-0
#define     LOG_fChannelDelayTimeMask 0x3FFF
#define     LOG_fChannelDelayTimeShift 0
#define LOG_fLogic                               2      // 8 Bits, Bit 7-0
#define LOG_fCalculate                           3      // 2 Bits, Bit 1-0
#define     LOG_fCalculateMask 0x03
#define     LOG_fCalculateShift 0
#define LOG_fDisable                             3      // 1 Bit, Bit 2
#define     LOG_fDisableMask 0x04
#define     LOG_fDisableShift 2
#define LOG_fTGate                               3      // 1 Bit, Bit 4
#define     LOG_fTGateMask 0x10
#define     LOG_fTGateShift 4
#define LOG_fOInternalOn                         3      // 1 Bit, Bit 5
#define     LOG_fOInternalOnMask 0x20
#define     LOG_fOInternalOnShift 5
#define LOG_fOInternalOff                        3      // 1 Bit, Bit 6
#define     LOG_fOInternalOffMask 0x40
#define     LOG_fOInternalOffShift 6
#define LOG_fTrigger                             4      // 8 Bits, Bit 7-0
#define LOG_fTriggerE1                           4      // 1 Bit, Bit 0
#define     LOG_fTriggerE1Mask 0x01
#define     LOG_fTriggerE1Shift 0
#define LOG_fTriggerE2                           4      // 1 Bit, Bit 1
#define     LOG_fTriggerE2Mask 0x02
#define     LOG_fTriggerE2Shift 1
#define LOG_fTriggerI1                           4      // 1 Bit, Bit 2
#define     LOG_fTriggerI1Mask 0x04
#define     LOG_fTriggerI1Shift 2
#define LOG_fTriggerI2                           4      // 1 Bit, Bit 3
#define     LOG_fTriggerI2Mask 0x08
#define     LOG_fTriggerI2Shift 3
#define LOG_fTriggerTime                         4      // 8 Bits, Bit 7-0
#define LOG_fTriggerGateClose                    5      // 2 Bits, Bit 7-6
#define     LOG_fTriggerGateCloseMask 0xC0
#define     LOG_fTriggerGateCloseShift 6
#define LOG_fTriggerGateOpen                     5      // 2 Bits, Bit 5-4
#define     LOG_fTriggerGateOpenMask 0x30
#define     LOG_fTriggerGateOpenShift 4
#define LOG_fE1ConvertInt                        6      // 4 Bits, Bit 7-4
#define     LOG_fE1ConvertIntMask 0xF0
#define     LOG_fE1ConvertIntShift 4
#define LOG_fE1Convert                           6      // 4 Bits, Bit 7-4
#define     LOG_fE1ConvertMask 0xF0
#define     LOG_fE1ConvertShift 4
#define LOG_fE1ConvertFloat                      6      // 4 Bits, Bit 7-4
#define     LOG_fE1ConvertFloatMask 0xF0
#define     LOG_fE1ConvertFloatShift 4
#define LOG_fE1ConvertSpecial                    6      // 4 Bits, Bit 7-4
#define     LOG_fE1ConvertSpecialMask 0xF0
#define     LOG_fE1ConvertSpecialShift 4
#define LOG_fE1ConvertBool                       6      // 4 Bits, Bit 7-4
#define     LOG_fE1ConvertBoolMask 0xF0
#define     LOG_fE1ConvertBoolShift 4
#define LOG_fE1                                  6      // 2 Bits, Bit 1-0
#define     LOG_fE1Mask 0x03
#define     LOG_fE1Shift 0
#define LOG_fE1Dpt                               7      // 8 Bits, Bit 7-0
#define LOG_fE1RepeatBase                        8      // 2 Bits, Bit 7-6
#define     LOG_fE1RepeatBaseMask 0xC0
#define     LOG_fE1RepeatBaseShift 6
#define LOG_fE1RepeatTime                        8      // 14 Bits, Bit 13-0
#define     LOG_fE1RepeatTimeMask 0x3FFF
#define     LOG_fE1RepeatTimeShift 0
#define LOG_fE1OtherKO                          10      // uint16_t
#define LOG_fE1OtherKORel                       10      // int16_t
#define LOG_fE1Default                          12      // 2 Bits, Bit 1-0
#define     LOG_fE1DefaultMask 0x03
#define     LOG_fE1DefaultShift 0
#define LOG_fE1DefaultExt                       12      // 2 Bits, Bit 1-0
#define     LOG_fE1DefaultExtMask 0x03
#define     LOG_fE1DefaultExtShift 0
#define LOG_fE1DefaultEEPROM                    12      // 1 Bit, Bit 2
#define     LOG_fE1DefaultEEPROMMask 0x04
#define     LOG_fE1DefaultEEPROMShift 2
#define LOG_fE1DefaultRepeat                    12      // 1 Bit, Bit 3
#define     LOG_fE1DefaultRepeatMask 0x08
#define     LOG_fE1DefaultRepeatShift 3
#define LOG_fE1UseOtherKO                       12      // 2 Bits, Bit 5-4
#define     LOG_fE1UseOtherKOMask 0x30
#define     LOG_fE1UseOtherKOShift 4
#define LOG_fE1LowDelta                         13      // int32_t
#define LOG_fE1HighDelta                        17      // int32_t
#define LOG_fE1LowDeltaFloat                    13      // float (4 Byte)
#define LOG_fE1HighDeltaFloat                   17      // float (4 Byte)
#define LOG_fE1LowDeltaDouble                   13      // float (4 Byte)
#define LOG_fE1HighDeltaDouble                  17      // float (4 Byte)
#define LOG_fE1Low0Valid                        20      // 1 Bit, Bit 7
#define     LOG_fE1Low0ValidMask 0x80
#define     LOG_fE1Low0ValidShift 7
#define LOG_fE1Low1Valid                        20      // 1 Bit, Bit 6
#define     LOG_fE1Low1ValidMask 0x40
#define     LOG_fE1Low1ValidShift 6
#define LOG_fE1Low2Valid                        20      // 1 Bit, Bit 5
#define     LOG_fE1Low2ValidMask 0x20
#define     LOG_fE1Low2ValidShift 5
#define LOG_fE1Low3Valid                        20      // 1 Bit, Bit 4
#define     LOG_fE1Low3ValidMask 0x10
#define     LOG_fE1Low3ValidShift 4
#define LOG_fE1Low4Valid                        20      // 1 Bit, Bit 3
#define     LOG_fE1Low4ValidMask 0x08
#define     LOG_fE1Low4ValidShift 3
#define LOG_fE1Low5Valid                        20      // 1 Bit, Bit 2
#define     LOG_fE1Low5ValidMask 0x04
#define     LOG_fE1Low5ValidShift 2
#define LOG_fE1Low6Valid                        20      // 1 Bit, Bit 1
#define     LOG_fE1Low6ValidMask 0x02
#define     LOG_fE1Low6ValidShift 1
#define LOG_fE1Low0Dpt2                         13      // 8 Bits, Bit 7-0
#define LOG_fE1Low1Dpt2                         14      // 8 Bits, Bit 7-0
#define LOG_fE1Low2Dpt2                         15      // 8 Bits, Bit 7-0
#define LOG_fE1Low3Dpt2                         16      // 8 Bits, Bit 7-0
#define LOG_fE1LowDpt2Fix                       13      // 8 Bits, Bit 7-0
#define LOG_fE1Low0Dpt3Dir                      13      // 5 Bits, Bit 7-3
#define     LOG_fE1Low0Dpt3DirMask 0xF8
#define     LOG_fE1Low0Dpt3DirShift 3
#define LOG_fE1Low0Dpt3Dim                      13      // 3 Bits, Bit 2-0
#define     LOG_fE1Low0Dpt3DimMask 0x07
#define     LOG_fE1Low0Dpt3DimShift 0
#define LOG_fE1Low1Dpt3Dir                      14      // 5 Bits, Bit 7-3
#define     LOG_fE1Low1Dpt3DirMask 0xF8
#define     LOG_fE1Low1Dpt3DirShift 3
#define LOG_fE1Low1Dpt3Dim                      14      // 3 Bits, Bit 2-0
#define     LOG_fE1Low1Dpt3DimMask 0x07
#define     LOG_fE1Low1Dpt3DimShift 0
#define LOG_fE1Low2Dpt3Dir                      15      // 5 Bits, Bit 7-3
#define     LOG_fE1Low2Dpt3DirMask 0xF8
#define     LOG_fE1Low2Dpt3DirShift 3
#define LOG_fE1Low2Dpt3Dim                      15      // 3 Bits, Bit 2-0
#define     LOG_fE1Low2Dpt3DimMask 0x07
#define     LOG_fE1Low2Dpt3DimShift 0
#define LOG_fE1Low3Dpt3Dir                      16      // 5 Bits, Bit 7-3
#define     LOG_fE1Low3Dpt3DirMask 0xF8
#define     LOG_fE1Low3Dpt3DirShift 3
#define LOG_fE1Low3Dpt3Dim                      16      // 3 Bits, Bit 2-0
#define     LOG_fE1Low3Dpt3DimMask 0x07
#define     LOG_fE1Low3Dpt3DimShift 0
#define LOG_fE1LowDpt3FixDir                    13      // 5 Bits, Bit 7-3
#define     LOG_fE1LowDpt3FixDirMask 0xF8
#define     LOG_fE1LowDpt3FixDirShift 3
#define LOG_fE1LowDpt3FixDim                    13      // 3 Bits, Bit 2-0
#define     LOG_fE1LowDpt3FixDimMask 0x07
#define     LOG_fE1LowDpt3FixDimShift 0
#define LOG_fE1LowDpt5                          13      // uint8_t
#define LOG_fE1HighDpt5                         17      // uint8_t
#define LOG_fE1Low0Dpt5In                       13      // uint8_t
#define LOG_fE1Low1Dpt5In                       14      // uint8_t
#define LOG_fE1Low2Dpt5In                       15      // uint8_t
#define LOG_fE1Low3Dpt5In                       16      // uint8_t
#define LOG_fE1Low4Dpt5In                       17      // uint8_t
#define LOG_fE1Low5Dpt5In                       18      // uint8_t
#define LOG_fE1Low6Dpt5In                       19      // uint8_t
#define LOG_fE1LowDpt5Fix                       13      // uint8_t
#define LOG_fE1LowDpt5001                       13      // uint8_t
#define LOG_fE1HighDpt5001                      17      // uint8_t
#define LOG_fE1Low0Dpt5xIn                      13      // uint8_t
#define LOG_fE1Low1Dpt5xIn                      14      // uint8_t
#define LOG_fE1Low2Dpt5xIn                      15      // uint8_t
#define LOG_fE1Low3Dpt5xIn                      16      // uint8_t
#define LOG_fE1Low4Dpt5xIn                      17      // uint8_t
#define LOG_fE1Low5Dpt5xIn                      18      // uint8_t
#define LOG_fE1Low6Dpt5xIn                      19      // uint8_t
#define LOG_fE1LowDpt5xFix                      13      // uint8_t
#define LOG_fE1LowDpt6                          13      // int8_t
#define LOG_fE1HighDpt6                         17      // int8_t
#define LOG_fE1Low0Dpt6In                       13      // int8_t
#define LOG_fE1Low1Dpt6In                       14      // int8_t
#define LOG_fE1Low2Dpt6In                       15      // int8_t
#define LOG_fE1Low3Dpt6In                       16      // int8_t
#define LOG_fE1Low4Dpt6In                       17      // int8_t
#define LOG_fE1Low5Dpt6In                       18      // int8_t
#define LOG_fE1Low6Dpt6In                       19      // int8_t
#define LOG_fE1LowDpt6Fix                       13      // int8_t
#define LOG_fE1LowDpt7                          13      // uint16_t
#define LOG_fE1HighDpt7                         17      // uint16_t
#define LOG_fE1Low0Dpt7In                       13      // uint16_t
#define LOG_fE1Low1Dpt7In                       15      // uint16_t
#define LOG_fE1Low2Dpt7In                       17      // uint16_t
#define LOG_fE1LowDpt7Fix                       13      // uint16_t
#define LOG_fE1LowDpt8                          13      // int16_t
#define LOG_fE1HighDpt8                         17      // int16_t
#define LOG_fE1Low0Dpt8In                       13      // int16_t
#define LOG_fE1Low1Dpt8In                       15      // int16_t
#define LOG_fE1Low2Dpt8In                       17      // int16_t
#define LOG_fE1LowDpt8Fix                       13      // int16_t
#define LOG_fE1LowDpt9                          13      // float (4 Byte)
#define LOG_fE1HighDpt9                         17      // float (4 Byte)
#define LOG_fE1LowDpt9Fix                       13      // float (4 Byte)
#define LOG_fE1LowDpt12                         13      // uint32_t
#define LOG_fE1HighDpt12                        17      // uint32_t
#define LOG_fE1LowDpt12Fix                      13      // uint32_t
#define LOG_fE1LowDpt13                         13      // int32_t
#define LOG_fE1HighDpt13                        17      // int32_t
#define LOG_fE1LowDpt13Fix                      13      // int32_t
#define LOG_fE1LowDpt14                         13      // float (4 Byte)
#define LOG_fE1HighDpt14                        17      // float (4 Byte)
#define LOG_fE1LowDpt14Fix                      13      // float (4 Byte)
#define LOG_fE1Low0Dpt17                        13      // 8 Bits, Bit 7-0
#define LOG_fE1Low1Dpt17                        14      // 8 Bits, Bit 7-0
#define LOG_fE1Low2Dpt17                        15      // 8 Bits, Bit 7-0
#define LOG_fE1Low3Dpt17                        16      // 8 Bits, Bit 7-0
#define LOG_fE1Low4Dpt17                        17      // 8 Bits, Bit 7-0
#define LOG_fE1Low5Dpt17                        18      // 8 Bits, Bit 7-0
#define LOG_fE1Low6Dpt17                        19      // 8 Bits, Bit 7-0
#define LOG_fE1Low7Dpt17                        20      // 8 Bits, Bit 7-0
#define LOG_fE1LowDpt17Fix                      13      // 8 Bits, Bit 7-0
#define LOG_fE1LowDptRGB                        13      // int32_t
#define LOG_fE1HighDptRGB                       17      // int32_t
#define LOG_fE1LowDptRGBFix                     13      // int32_t
#define LOG_fE2ConvertInt                       21      // 4 Bits, Bit 7-4
#define     LOG_fE2ConvertIntMask 0xF0
#define     LOG_fE2ConvertIntShift 4
#define LOG_fE2Convert                          21      // 4 Bits, Bit 7-4
#define     LOG_fE2ConvertMask 0xF0
#define     LOG_fE2ConvertShift 4
#define LOG_fE2ConvertFloat                     21      // 4 Bits, Bit 7-4
#define     LOG_fE2ConvertFloatMask 0xF0
#define     LOG_fE2ConvertFloatShift 4
#define LOG_fE2ConvertSpecial                   21      // 4 Bits, Bit 7-4
#define     LOG_fE2ConvertSpecialMask 0xF0
#define     LOG_fE2ConvertSpecialShift 4
#define LOG_fE2ConvertBool                      21      // 4 Bits, Bit 7-4
#define     LOG_fE2ConvertBoolMask 0xF0
#define     LOG_fE2ConvertBoolShift 4
#define LOG_fE2                                 21      // 2 Bits, Bit 1-0
#define     LOG_fE2Mask 0x03
#define     LOG_fE2Shift 0
#define LOG_fE2Dpt                              22      // 8 Bits, Bit 7-0
#define LOG_fE2RepeatBase                       23      // 2 Bits, Bit 7-6
#define     LOG_fE2RepeatBaseMask 0xC0
#define     LOG_fE2RepeatBaseShift 6
#define LOG_fE2RepeatTime                       23      // 14 Bits, Bit 13-0
#define     LOG_fE2RepeatTimeMask 0x3FFF
#define     LOG_fE2RepeatTimeShift 0
#define LOG_fE2OtherKO                          25      // uint16_t
#define LOG_fE2OtherKORel                       25      // int16_t
#define LOG_fE2Default                          27      // 2 Bits, Bit 1-0
#define     LOG_fE2DefaultMask 0x03
#define     LOG_fE2DefaultShift 0
#define LOG_fE2DefaultExt                       27      // 2 Bits, Bit 1-0
#define     LOG_fE2DefaultExtMask 0x03
#define     LOG_fE2DefaultExtShift 0
#define LOG_fE2DefaultEEPROM                    27      // 1 Bit, Bit 2
#define     LOG_fE2DefaultEEPROMMask 0x04
#define     LOG_fE2DefaultEEPROMShift 2
#define LOG_fE2DefaultRepeat                    27      // 1 Bit, Bit 3
#define     LOG_fE2DefaultRepeatMask 0x08
#define     LOG_fE2DefaultRepeatShift 3
#define LOG_fE2UseOtherKO                       27      // 2 Bits, Bit 5-4
#define     LOG_fE2UseOtherKOMask 0x30
#define     LOG_fE2UseOtherKOShift 4
#define LOG_fE2LowDelta                         28      // int32_t
#define LOG_fE2HighDelta                        32      // int32_t
#define LOG_fE2LowDeltaFloat                    28      // float (4 Byte)
#define LOG_fE2HighDeltaFloat                   32      // float (4 Byte)
#define LOG_fE2LowDeltaDouble                   28      // float (4 Byte)
#define LOG_fE2HighDeltaDouble                  32      // float (4 Byte)
#define LOG_fE2Low0Valid                        35      // 1 Bit, Bit 7
#define     LOG_fE2Low0ValidMask 0x80
#define     LOG_fE2Low0ValidShift 7
#define LOG_fE2Low1Valid                        35      // 1 Bit, Bit 6
#define     LOG_fE2Low1ValidMask 0x40
#define     LOG_fE2Low1ValidShift 6
#define LOG_fE2Low2Valid                        35      // 1 Bit, Bit 5
#define     LOG_fE2Low2ValidMask 0x20
#define     LOG_fE2Low2ValidShift 5
#define LOG_fE2Low3Valid                        35      // 1 Bit, Bit 4
#define     LOG_fE2Low3ValidMask 0x10
#define     LOG_fE2Low3ValidShift 4
#define LOG_fE2Low4Valid                        35      // 1 Bit, Bit 3
#define     LOG_fE2Low4ValidMask 0x08
#define     LOG_fE2Low4ValidShift 3
#define LOG_fE2Low5Valid                        35      // 1 Bit, Bit 2
#define     LOG_fE2Low5ValidMask 0x04
#define     LOG_fE2Low5ValidShift 2
#define LOG_fE2Low6Valid                        35      // 1 Bit, Bit 1
#define     LOG_fE2Low6ValidMask 0x02
#define     LOG_fE2Low6ValidShift 1
#define LOG_fE2Low0Dpt2                         28      // 8 Bits, Bit 7-0
#define LOG_fE2Low1Dpt2                         29      // 8 Bits, Bit 7-0
#define LOG_fE2Low2Dpt2                         30      // 8 Bits, Bit 7-0
#define LOG_fE2Low3Dpt2                         31      // 8 Bits, Bit 7-0
#define LOG_fE2LowDpt2Fix                       28      // 8 Bits, Bit 7-0
#define LOG_fE2Low0Dpt3Dir                      28      // 5 Bits, Bit 7-3
#define     LOG_fE2Low0Dpt3DirMask 0xF8
#define     LOG_fE2Low0Dpt3DirShift 3
#define LOG_fE2Low0Dpt3Dim                      28      // 3 Bits, Bit 2-0
#define     LOG_fE2Low0Dpt3DimMask 0x07
#define     LOG_fE2Low0Dpt3DimShift 0
#define LOG_fE2Low1Dpt3Dir                      29      // 5 Bits, Bit 7-3
#define     LOG_fE2Low1Dpt3DirMask 0xF8
#define     LOG_fE2Low1Dpt3DirShift 3
#define LOG_fE2Low1Dpt3Dim                      29      // 3 Bits, Bit 2-0
#define     LOG_fE2Low1Dpt3DimMask 0x07
#define     LOG_fE2Low1Dpt3DimShift 0
#define LOG_fE2Low2Dpt3Dir                      30      // 5 Bits, Bit 7-3
#define     LOG_fE2Low2Dpt3DirMask 0xF8
#define     LOG_fE2Low2Dpt3DirShift 3
#define LOG_fE2Low2Dpt3Dim                      30      // 3 Bits, Bit 2-0
#define     LOG_fE2Low2Dpt3DimMask 0x07
#define     LOG_fE2Low2Dpt3DimShift 0
#define LOG_fE2Low3Dpt3Dir                      31      // 5 Bits, Bit 7-3
#define     LOG_fE2Low3Dpt3DirMask 0xF8
#define     LOG_fE2Low3Dpt3DirShift 3
#define LOG_fE2Low3Dpt3Dim                      31      // 3 Bits, Bit 2-0
#define     LOG_fE2Low3Dpt3DimMask 0x07
#define     LOG_fE2Low3Dpt3DimShift 0
#define LOG_fE2LowDpt3FixDir                    28      // 5 Bits, Bit 7-3
#define     LOG_fE2LowDpt3FixDirMask 0xF8
#define     LOG_fE2LowDpt3FixDirShift 3
#define LOG_fE2LowDpt3FixDim                    28      // 3 Bits, Bit 2-0
#define     LOG_fE2LowDpt3FixDimMask 0x07
#define     LOG_fE2LowDpt3FixDimShift 0
#define LOG_fE2LowDpt5                          28      // uint8_t
#define LOG_fE2HighDpt5                         32      // uint8_t
#define LOG_fE2Low0Dpt5In                       28      // uint8_t
#define LOG_fE2Low1Dpt5In                       29      // uint8_t
#define LOG_fE2Low2Dpt5In                       30      // uint8_t
#define LOG_fE2Low3Dpt5In                       31      // uint8_t
#define LOG_fE2Low4Dpt5In                       32      // uint8_t
#define LOG_fE2Low5Dpt5In                       33      // uint8_t
#define LOG_fE2Low6Dpt5In                       34      // uint8_t
#define LOG_fE2LowDpt5Fix                       28      // uint8_t
#define LOG_fE2LowDpt5001                       28      // uint8_t
#define LOG_fE2HighDpt5001                      32      // uint8_t
#define LOG_fE2Low0Dpt5xIn                      28      // uint8_t
#define LOG_fE2Low1Dpt5xIn                      29      // uint8_t
#define LOG_fE2Low2Dpt5xIn                      30      // uint8_t
#define LOG_fE2Low3Dpt5xIn                      31      // uint8_t
#define LOG_fE2Low4Dpt5xIn                      32      // uint8_t
#define LOG_fE2Low5Dpt5xIn                      33      // uint8_t
#define LOG_fE2Low6Dpt5xIn                      34      // uint8_t
#define LOG_fE2LowDpt5xFix                      28      // uint8_t
#define LOG_fE2LowDpt6                          28      // int8_t
#define LOG_fE2HighDpt6                         32      // int8_t
#define LOG_fE2Low0Dpt6In                       28      // int8_t
#define LOG_fE2Low1Dpt6In                       29      // int8_t
#define LOG_fE2Low2Dpt6In                       30      // int8_t
#define LOG_fE2Low3Dpt6In                       31      // int8_t
#define LOG_fE2Low4Dpt6In                       32      // int8_t
#define LOG_fE2Low5Dpt6In                       33      // int8_t
#define LOG_fE2Low6Dpt6In                       34      // int8_t
#define LOG_fE2LowDpt6Fix                       28      // int8_t
#define LOG_fE2LowDpt7                          28      // uint16_t
#define LOG_fE2HighDpt7                         32      // uint16_t
#define LOG_fE2Low0Dpt7In                       28      // uint16_t
#define LOG_fE2Low1Dpt7In                       30      // uint16_t
#define LOG_fE2Low2Dpt7In                       32      // uint16_t
#define LOG_fE2LowDpt7Fix                       28      // uint16_t
#define LOG_fE2LowDpt8                          28      // int16_t
#define LOG_fE2HighDpt8                         32      // int16_t
#define LOG_fE2Low0Dpt8In                       28      // int16_t
#define LOG_fE2Low1Dpt8In                       30      // int16_t
#define LOG_fE2Low2Dpt8In                       32      // int16_t
#define LOG_fE2LowDpt8Fix                       28      // int16_t
#define LOG_fE2LowDpt9                          28      // float (4 Byte)
#define LOG_fE2HighDpt9                         32      // float (4 Byte)
#define LOG_fE2LowDpt9Fix                       28      // float (4 Byte)
#define LOG_fE2LowDpt12                         28      // uint32_t
#define LOG_fE2HighDpt12                        32      // uint32_t
#define LOG_fE2LowDpt12Fix                      28      // uint32_t
#define LOG_fE2LowDpt13                         28      // int32_t
#define LOG_fE2HighDpt13                        32      // int32_t
#define LOG_fE2LowDpt13Fix                      28      // int32_t
#define LOG_fE2LowDpt14                         28      // float (4 Byte)
#define LOG_fE2HighDpt14                        32      // float (4 Byte)
#define LOG_fE2LowDpt14Fix                      28      // float (4 Byte)
#define LOG_fE2Low0Dpt17                        28      // 8 Bits, Bit 7-0
#define LOG_fE2Low1Dpt17                        29      // 8 Bits, Bit 7-0
#define LOG_fE2Low2Dpt17                        30      // 8 Bits, Bit 7-0
#define LOG_fE2Low3Dpt17                        31      // 8 Bits, Bit 7-0
#define LOG_fE2Low4Dpt17                        32      // 8 Bits, Bit 7-0
#define LOG_fE2Low5Dpt17                        33      // 8 Bits, Bit 7-0
#define LOG_fE2Low6Dpt17                        34      // 8 Bits, Bit 7-0
#define LOG_fE2Low7Dpt17                        35      // 8 Bits, Bit 7-0
#define LOG_fE2LowDpt17Fix                      28      // 8 Bits, Bit 7-0
#define LOG_fE2LowDptRGB                        28      // int32_t
#define LOG_fE2HighDptRGB                       32      // int32_t
#define LOG_fE2LowDptRGBFix                     28      // int32_t
#define LOG_fTd1DuskDawn                         6      // 4 Bits, Bit 7-4
#define     LOG_fTd1DuskDawnMask 0xF0
#define     LOG_fTd1DuskDawnShift 4
#define LOG_fTd2DuskDawn                         6      // 4 Bits, Bit 3-0
#define     LOG_fTd2DuskDawnMask 0x0F
#define     LOG_fTd2DuskDawnShift 0
#define LOG_fTd3DuskDawn                         7      // 4 Bits, Bit 7-4
#define     LOG_fTd3DuskDawnMask 0xF0
#define     LOG_fTd3DuskDawnShift 4
#define LOG_fTd4DuskDawn                         7      // 4 Bits, Bit 3-0
#define     LOG_fTd4DuskDawnMask 0x0F
#define     LOG_fTd4DuskDawnShift 0
#define LOG_fTd5DuskDawn                         8      // 4 Bits, Bit 7-4
#define     LOG_fTd5DuskDawnMask 0xF0
#define     LOG_fTd5DuskDawnShift 4
#define LOG_fTd6DuskDawn                         8      // 4 Bits, Bit 3-0
#define     LOG_fTd6DuskDawnMask 0x0F
#define     LOG_fTd6DuskDawnShift 0
#define LOG_fTd7DuskDawn                         9      // 4 Bits, Bit 7-4
#define     LOG_fTd7DuskDawnMask 0xF0
#define     LOG_fTd7DuskDawnShift 4
#define LOG_fTd8DuskDawn                         9      // 4 Bits, Bit 3-0
#define     LOG_fTd8DuskDawnMask 0x0F
#define     LOG_fTd8DuskDawnShift 0
#define LOG_fTYearDay                           10      // 2 Bits, Bit 7-6
#define     LOG_fTYearDayMask 0xC0
#define     LOG_fTYearDayShift 6
#define LOG_fTHoliday                           10      // 2 Bits, Bit 5-4
#define     LOG_fTHolidayMask 0x30
#define     LOG_fTHolidayShift 4
#define LOG_fTRestoreState                      10      // 2 Bits, Bit 3-2
#define     LOG_fTRestoreStateMask 0x0C
#define     LOG_fTRestoreStateShift 2
#define LOG_fTVacation                          10      // 2 Bits, Bit 1-0
#define     LOG_fTVacationMask 0x03
#define     LOG_fTVacationShift 0
#define LOG_fTd1ValueNum                        11      // uint8_t
#define LOG_fTd2ValueNum                        12      // uint8_t
#define LOG_fTd3ValueNum                        13      // uint8_t
#define LOG_fTd4ValueNum                        14      // uint8_t
#define LOG_fTd5ValueNum                        15      // uint8_t
#define LOG_fTd6ValueNum                        16      // uint8_t
#define LOG_fTd7ValueNum                        17      // uint8_t
#define LOG_fTd8ValueNum                        18      // uint8_t
#define LOG_fTd1Value                           20      // 1 Bit, Bit 7
#define     LOG_fTd1ValueMask 0x80
#define     LOG_fTd1ValueShift 7
#define LOG_fTd1Degree                          20      // 6 Bits, Bit 6-1
#define     LOG_fTd1DegreeMask 0x7E
#define     LOG_fTd1DegreeShift 1
#define LOG_fTd1HourAbs                         20      // 5 Bits, Bit 5-1
#define     LOG_fTd1HourAbsMask 0x3E
#define     LOG_fTd1HourAbsShift 1
#define LOG_fTd1HourRel                         20      // 5 Bits, Bit 5-1
#define     LOG_fTd1HourRelMask 0x3E
#define     LOG_fTd1HourRelShift 1
#define LOG_fTd1HourRelShort                    20      // 5 Bits, Bit 5-1
#define     LOG_fTd1HourRelShortMask 0x3E
#define     LOG_fTd1HourRelShortShift 1
#define LOG_fTd1MinuteAbs                       20      // 6 Bits, Bit 0--5
#define LOG_fTd1MinuteRel                       20      // 6 Bits, Bit 0--5
#define LOG_fTd1Weekday                         21      // 3 Bits, Bit 2-0
#define     LOG_fTd1WeekdayMask 0x07
#define     LOG_fTd1WeekdayShift 0
#define LOG_fTd2Value                           22      // 1 Bit, Bit 7
#define     LOG_fTd2ValueMask 0x80
#define     LOG_fTd2ValueShift 7
#define LOG_fTd2Degree                          22      // 6 Bits, Bit 6-1
#define     LOG_fTd2DegreeMask 0x7E
#define     LOG_fTd2DegreeShift 1
#define LOG_fTd2HourAbs                         22      // 5 Bits, Bit 5-1
#define     LOG_fTd2HourAbsMask 0x3E
#define     LOG_fTd2HourAbsShift 1
#define LOG_fTd2HourRel                         22      // 5 Bits, Bit 5-1
#define     LOG_fTd2HourRelMask 0x3E
#define     LOG_fTd2HourRelShift 1
#define LOG_fTd2HourRelShort                    22      // 5 Bits, Bit 5-1
#define     LOG_fTd2HourRelShortMask 0x3E
#define     LOG_fTd2HourRelShortShift 1
#define LOG_fTd2MinuteAbs                       22      // 6 Bits, Bit 0--5
#define LOG_fTd2MinuteRel                       22      // 6 Bits, Bit 0--5
#define LOG_fTd2Weekday                         23      // 3 Bits, Bit 2-0
#define     LOG_fTd2WeekdayMask 0x07
#define     LOG_fTd2WeekdayShift 0
#define LOG_fTd3Value                           24      // 1 Bit, Bit 7
#define     LOG_fTd3ValueMask 0x80
#define     LOG_fTd3ValueShift 7
#define LOG_fTd3Degree                          24      // 6 Bits, Bit 6-1
#define     LOG_fTd3DegreeMask 0x7E
#define     LOG_fTd3DegreeShift 1
#define LOG_fTd3HourAbs                         24      // 5 Bits, Bit 5-1
#define     LOG_fTd3HourAbsMask 0x3E
#define     LOG_fTd3HourAbsShift 1
#define LOG_fTd3HourRel                         24      // 5 Bits, Bit 5-1
#define     LOG_fTd3HourRelMask 0x3E
#define     LOG_fTd3HourRelShift 1
#define LOG_fTd3HourRelShort                    24      // 5 Bits, Bit 5-1
#define     LOG_fTd3HourRelShortMask 0x3E
#define     LOG_fTd3HourRelShortShift 1
#define LOG_fTd3MinuteAbs                       24      // 6 Bits, Bit 0--5
#define LOG_fTd3MinuteRel                       24      // 6 Bits, Bit 0--5
#define LOG_fTd3Weekday                         25      // 3 Bits, Bit 2-0
#define     LOG_fTd3WeekdayMask 0x07
#define     LOG_fTd3WeekdayShift 0
#define LOG_fTd4Value                           26      // 1 Bit, Bit 7
#define     LOG_fTd4ValueMask 0x80
#define     LOG_fTd4ValueShift 7
#define LOG_fTd4Degree                          26      // 6 Bits, Bit 6-1
#define     LOG_fTd4DegreeMask 0x7E
#define     LOG_fTd4DegreeShift 1
#define LOG_fTd4HourAbs                         26      // 5 Bits, Bit 5-1
#define     LOG_fTd4HourAbsMask 0x3E
#define     LOG_fTd4HourAbsShift 1
#define LOG_fTd4HourRel                         26      // 5 Bits, Bit 5-1
#define     LOG_fTd4HourRelMask 0x3E
#define     LOG_fTd4HourRelShift 1
#define LOG_fTd4HourRelShort                    26      // 5 Bits, Bit 5-1
#define     LOG_fTd4HourRelShortMask 0x3E
#define     LOG_fTd4HourRelShortShift 1
#define LOG_fTd4MinuteAbs                       26      // 6 Bits, Bit 0--5
#define LOG_fTd4MinuteRel                       26      // 6 Bits, Bit 0--5
#define LOG_fTd4Weekday                         27      // 3 Bits, Bit 2-0
#define     LOG_fTd4WeekdayMask 0x07
#define     LOG_fTd4WeekdayShift 0
#define LOG_fTd5Value                           28      // 1 Bit, Bit 7
#define     LOG_fTd5ValueMask 0x80
#define     LOG_fTd5ValueShift 7
#define LOG_fTd5Degree                          28      // 6 Bits, Bit 6-1
#define     LOG_fTd5DegreeMask 0x7E
#define     LOG_fTd5DegreeShift 1
#define LOG_fTd5HourAbs                         28      // 5 Bits, Bit 5-1
#define     LOG_fTd5HourAbsMask 0x3E
#define     LOG_fTd5HourAbsShift 1
#define LOG_fTd5HourRel                         28      // 5 Bits, Bit 5-1
#define     LOG_fTd5HourRelMask 0x3E
#define     LOG_fTd5HourRelShift 1
#define LOG_fTd5HourRelShort                    28      // 5 Bits, Bit 5-1
#define     LOG_fTd5HourRelShortMask 0x3E
#define     LOG_fTd5HourRelShortShift 1
#define LOG_fTd5MinuteAbs                       28      // 6 Bits, Bit 0--5
#define LOG_fTd5MinuteRel                       28      // 6 Bits, Bit 0--5
#define LOG_fTd5Weekday                         29      // 3 Bits, Bit 2-0
#define     LOG_fTd5WeekdayMask 0x07
#define     LOG_fTd5WeekdayShift 0
#define LOG_fTd6Value                           30      // 1 Bit, Bit 7
#define     LOG_fTd6ValueMask 0x80
#define     LOG_fTd6ValueShift 7
#define LOG_fTd6Degree                          30      // 6 Bits, Bit 6-1
#define     LOG_fTd6DegreeMask 0x7E
#define     LOG_fTd6DegreeShift 1
#define LOG_fTd6HourAbs                         30      // 5 Bits, Bit 5-1
#define     LOG_fTd6HourAbsMask 0x3E
#define     LOG_fTd6HourAbsShift 1
#define LOG_fTd6HourRel                         30      // 5 Bits, Bit 5-1
#define     LOG_fTd6HourRelMask 0x3E
#define     LOG_fTd6HourRelShift 1
#define LOG_fTd6HourRelShort                    30      // 5 Bits, Bit 5-1
#define     LOG_fTd6HourRelShortMask 0x3E
#define     LOG_fTd6HourRelShortShift 1
#define LOG_fTd6MinuteAbs                       30      // 6 Bits, Bit 0--5
#define LOG_fTd6MinuteRel                       30      // 6 Bits, Bit 0--5
#define LOG_fTd6Weekday                         31      // 3 Bits, Bit 2-0
#define     LOG_fTd6WeekdayMask 0x07
#define     LOG_fTd6WeekdayShift 0
#define LOG_fTd7Value                           32      // 1 Bit, Bit 7
#define     LOG_fTd7ValueMask 0x80
#define     LOG_fTd7ValueShift 7
#define LOG_fTd7Degree                          32      // 6 Bits, Bit 6-1
#define     LOG_fTd7DegreeMask 0x7E
#define     LOG_fTd7DegreeShift 1
#define LOG_fTd7HourAbs                         32      // 5 Bits, Bit 5-1
#define     LOG_fTd7HourAbsMask 0x3E
#define     LOG_fTd7HourAbsShift 1
#define LOG_fTd7HourRel                         32      // 5 Bits, Bit 5-1
#define     LOG_fTd7HourRelMask 0x3E
#define     LOG_fTd7HourRelShift 1
#define LOG_fTd7HourRelShort                    32      // 5 Bits, Bit 5-1
#define     LOG_fTd7HourRelShortMask 0x3E
#define     LOG_fTd7HourRelShortShift 1
#define LOG_fTd7MinuteAbs                       32      // 6 Bits, Bit 0--5
#define LOG_fTd7MinuteRel                       32      // 6 Bits, Bit 0--5
#define LOG_fTd7Weekday                         33      // 3 Bits, Bit 2-0
#define     LOG_fTd7WeekdayMask 0x07
#define     LOG_fTd7WeekdayShift 0
#define LOG_fTd8Value                           34      // 1 Bit, Bit 7
#define     LOG_fTd8ValueMask 0x80
#define     LOG_fTd8ValueShift 7
#define LOG_fTd8Degree                          34      // 6 Bits, Bit 6-1
#define     LOG_fTd8DegreeMask 0x7E
#define     LOG_fTd8DegreeShift 1
#define LOG_fTd8HourAbs                         34      // 5 Bits, Bit 5-1
#define     LOG_fTd8HourAbsMask 0x3E
#define     LOG_fTd8HourAbsShift 1
#define LOG_fTd8HourRel                         34      // 5 Bits, Bit 5-1
#define     LOG_fTd8HourRelMask 0x3E
#define     LOG_fTd8HourRelShift 1
#define LOG_fTd8HourRelShort                    34      // 5 Bits, Bit 5-1
#define     LOG_fTd8HourRelShortMask 0x3E
#define     LOG_fTd8HourRelShortShift 1
#define LOG_fTd8MinuteAbs                       34      // 6 Bits, Bit 0--5
#define LOG_fTd8MinuteRel                       34      // 6 Bits, Bit 0--5
#define LOG_fTd8Weekday                         35      // 3 Bits, Bit 2-0
#define     LOG_fTd8WeekdayMask 0x07
#define     LOG_fTd8WeekdayShift 0
#define LOG_fTy1Weekday1                        28      // 1 Bit, Bit 7
#define     LOG_fTy1Weekday1Mask 0x80
#define     LOG_fTy1Weekday1Shift 7
#define LOG_fTy1Weekday2                        28      // 1 Bit, Bit 6
#define     LOG_fTy1Weekday2Mask 0x40
#define     LOG_fTy1Weekday2Shift 6
#define LOG_fTy1Weekday3                        28      // 1 Bit, Bit 5
#define     LOG_fTy1Weekday3Mask 0x20
#define     LOG_fTy1Weekday3Shift 5
#define LOG_fTy1Weekday4                        28      // 1 Bit, Bit 4
#define     LOG_fTy1Weekday4Mask 0x10
#define     LOG_fTy1Weekday4Shift 4
#define LOG_fTy1Weekday5                        28      // 1 Bit, Bit 3
#define     LOG_fTy1Weekday5Mask 0x08
#define     LOG_fTy1Weekday5Shift 3
#define LOG_fTy1Weekday6                        28      // 1 Bit, Bit 2
#define     LOG_fTy1Weekday6Mask 0x04
#define     LOG_fTy1Weekday6Shift 2
#define LOG_fTy1Weekday7                        28      // 1 Bit, Bit 1
#define     LOG_fTy1Weekday7Mask 0x02
#define     LOG_fTy1Weekday7Shift 1
#define LOG_fTy1Day                             28      // 7 Bits, Bit 7-1
#define     LOG_fTy1DayMask 0xFE
#define     LOG_fTy1DayShift 1
#define LOG_fTy1IsWeekday                       28      // 1 Bit, Bit 0
#define     LOG_fTy1IsWeekdayMask 0x01
#define     LOG_fTy1IsWeekdayShift 0
#define LOG_fTy1Month                           29      // 4 Bits, Bit 7-4
#define     LOG_fTy1MonthMask 0xF0
#define     LOG_fTy1MonthShift 4
#define LOG_fTy2Weekday1                        30      // 1 Bit, Bit 7
#define     LOG_fTy2Weekday1Mask 0x80
#define     LOG_fTy2Weekday1Shift 7
#define LOG_fTy2Weekday2                        30      // 1 Bit, Bit 6
#define     LOG_fTy2Weekday2Mask 0x40
#define     LOG_fTy2Weekday2Shift 6
#define LOG_fTy2Weekday3                        30      // 1 Bit, Bit 5
#define     LOG_fTy2Weekday3Mask 0x20
#define     LOG_fTy2Weekday3Shift 5
#define LOG_fTy2Weekday4                        30      // 1 Bit, Bit 4
#define     LOG_fTy2Weekday4Mask 0x10
#define     LOG_fTy2Weekday4Shift 4
#define LOG_fTy2Weekday5                        30      // 1 Bit, Bit 3
#define     LOG_fTy2Weekday5Mask 0x08
#define     LOG_fTy2Weekday5Shift 3
#define LOG_fTy2Weekday6                        30      // 1 Bit, Bit 2
#define     LOG_fTy2Weekday6Mask 0x04
#define     LOG_fTy2Weekday6Shift 2
#define LOG_fTy2Weekday7                        30      // 1 Bit, Bit 1
#define     LOG_fTy2Weekday7Mask 0x02
#define     LOG_fTy2Weekday7Shift 1
#define LOG_fTy2Day                             30      // 7 Bits, Bit 7-1
#define     LOG_fTy2DayMask 0xFE
#define     LOG_fTy2DayShift 1
#define LOG_fTy2IsWeekday                       30      // 1 Bit, Bit 0
#define     LOG_fTy2IsWeekdayMask 0x01
#define     LOG_fTy2IsWeekdayShift 0
#define LOG_fTy2Month                           31      // 4 Bits, Bit 7-4
#define     LOG_fTy2MonthMask 0xF0
#define     LOG_fTy2MonthShift 4
#define LOG_fTy3Weekday1                        32      // 1 Bit, Bit 7
#define     LOG_fTy3Weekday1Mask 0x80
#define     LOG_fTy3Weekday1Shift 7
#define LOG_fTy3Weekday2                        32      // 1 Bit, Bit 6
#define     LOG_fTy3Weekday2Mask 0x40
#define     LOG_fTy3Weekday2Shift 6
#define LOG_fTy3Weekday3                        32      // 1 Bit, Bit 5
#define     LOG_fTy3Weekday3Mask 0x20
#define     LOG_fTy3Weekday3Shift 5
#define LOG_fTy3Weekday4                        32      // 1 Bit, Bit 4
#define     LOG_fTy3Weekday4Mask 0x10
#define     LOG_fTy3Weekday4Shift 4
#define LOG_fTy3Weekday5                        32      // 1 Bit, Bit 3
#define     LOG_fTy3Weekday5Mask 0x08
#define     LOG_fTy3Weekday5Shift 3
#define LOG_fTy3Weekday6                        32      // 1 Bit, Bit 2
#define     LOG_fTy3Weekday6Mask 0x04
#define     LOG_fTy3Weekday6Shift 2
#define LOG_fTy3Weekday7                        32      // 1 Bit, Bit 1
#define     LOG_fTy3Weekday7Mask 0x02
#define     LOG_fTy3Weekday7Shift 1
#define LOG_fTy3Day                             32      // 7 Bits, Bit 7-1
#define     LOG_fTy3DayMask 0xFE
#define     LOG_fTy3DayShift 1
#define LOG_fTy3IsWeekday                       32      // 1 Bit, Bit 0
#define     LOG_fTy3IsWeekdayMask 0x01
#define     LOG_fTy3IsWeekdayShift 0
#define LOG_fTy3Month                           33      // 4 Bits, Bit 7-4
#define     LOG_fTy3MonthMask 0xF0
#define     LOG_fTy3MonthShift 4
#define LOG_fTy4Weekday1                        34      // 1 Bit, Bit 7
#define     LOG_fTy4Weekday1Mask 0x80
#define     LOG_fTy4Weekday1Shift 7
#define LOG_fTy4Weekday2                        34      // 1 Bit, Bit 6
#define     LOG_fTy4Weekday2Mask 0x40
#define     LOG_fTy4Weekday2Shift 6
#define LOG_fTy4Weekday3                        34      // 1 Bit, Bit 5
#define     LOG_fTy4Weekday3Mask 0x20
#define     LOG_fTy4Weekday3Shift 5
#define LOG_fTy4Weekday4                        34      // 1 Bit, Bit 4
#define     LOG_fTy4Weekday4Mask 0x10
#define     LOG_fTy4Weekday4Shift 4
#define LOG_fTy4Weekday5                        34      // 1 Bit, Bit 3
#define     LOG_fTy4Weekday5Mask 0x08
#define     LOG_fTy4Weekday5Shift 3
#define LOG_fTy4Weekday6                        34      // 1 Bit, Bit 2
#define     LOG_fTy4Weekday6Mask 0x04
#define     LOG_fTy4Weekday6Shift 2
#define LOG_fTy4Weekday7                        34      // 1 Bit, Bit 1
#define     LOG_fTy4Weekday7Mask 0x02
#define     LOG_fTy4Weekday7Shift 1
#define LOG_fTy4Day                             34      // 7 Bits, Bit 7-1
#define     LOG_fTy4DayMask 0xFE
#define     LOG_fTy4DayShift 1
#define LOG_fTy4IsWeekday                       34      // 1 Bit, Bit 0
#define     LOG_fTy4IsWeekdayMask 0x01
#define     LOG_fTy4IsWeekdayShift 0
#define LOG_fTy4Month                           35      // 4 Bits, Bit 7-4
#define     LOG_fTy4MonthMask 0xF0
#define     LOG_fTy4MonthShift 4
#define LOG_fI1                                 36      // 2 Bits, Bit 7-6
#define     LOG_fI1Mask 0xC0
#define     LOG_fI1Shift 6
#define LOG_fI1Kind                             36      // 2 Bits, Bit 5-4
#define     LOG_fI1KindMask 0x30
#define     LOG_fI1KindShift 4
#define LOG_fI1AsTrigger                        36      // 1 Bit, Bit 3
#define     LOG_fI1AsTriggerMask 0x08
#define     LOG_fI1AsTriggerShift 3
#define LOG_fI1InternalInputType                36      // 1 Bit, Bit 2
#define     LOG_fI1InternalInputTypeMask 0x04
#define     LOG_fI1InternalInputTypeShift 2
#define LOG_fI1Function                         37      // uint8_t
#define LOG_fI1FunctionRel                      37      // int8_t
#define LOG_fI1StatusLed                        37      // 16 Bits, Bit 15-0
#define LOG_fI2                                 39      // 2 Bits, Bit 7-6
#define     LOG_fI2Mask 0xC0
#define     LOG_fI2Shift 6
#define LOG_fI2Kind                             39      // 2 Bits, Bit 5-4
#define     LOG_fI2KindMask 0x30
#define     LOG_fI2KindShift 4
#define LOG_fI2AsTrigger                        39      // 1 Bit, Bit 3
#define     LOG_fI2AsTriggerMask 0x08
#define     LOG_fI2AsTriggerShift 3
#define LOG_fI2InternalInputType                39      // 1 Bit, Bit 2
#define     LOG_fI2InternalInputTypeMask 0x04
#define     LOG_fI2InternalInputTypeShift 2
#define LOG_fI2Function                         40      // uint8_t
#define LOG_fI2FunctionRel                      40      // int8_t
#define LOG_fI2StatusLed                        40      // 16 Bits, Bit 15-0
#define LOG_fOStairtimeBase                     42      // 2 Bits, Bit 7-6
#define     LOG_fOStairtimeBaseMask 0xC0
#define     LOG_fOStairtimeBaseShift 6
#define LOG_fOStairtimeTime                     42      // 14 Bits, Bit 13-0
#define     LOG_fOStairtimeTimeMask 0x3FFF
#define     LOG_fOStairtimeTimeShift 0
#define LOG_fOBlinkBase                         44      // 2 Bits, Bit 7-6
#define     LOG_fOBlinkBaseMask 0xC0
#define     LOG_fOBlinkBaseShift 6
#define LOG_fOBlinkTime                         44      // 14 Bits, Bit 13-0
#define     LOG_fOBlinkTimeMask 0x3FFF
#define     LOG_fOBlinkTimeShift 0
#define LOG_fODelayOnBase                       46      // 2 Bits, Bit 7-6
#define     LOG_fODelayOnBaseMask 0xC0
#define     LOG_fODelayOnBaseShift 6
#define LOG_fODelayOnTime                       46      // 14 Bits, Bit 13-0
#define     LOG_fODelayOnTimeMask 0x3FFF
#define     LOG_fODelayOnTimeShift 0
#define LOG_fODelayOffBase                      48      // 2 Bits, Bit 7-6
#define     LOG_fODelayOffBaseMask 0xC0
#define     LOG_fODelayOffBaseShift 6
#define LOG_fODelayOffTime                      48      // 14 Bits, Bit 13-0
#define     LOG_fODelayOffTimeMask 0x3FFF
#define     LOG_fODelayOffTimeShift 0
#define LOG_fORepeatOnBase                      50      // 2 Bits, Bit 7-6
#define     LOG_fORepeatOnBaseMask 0xC0
#define     LOG_fORepeatOnBaseShift 6
#define LOG_fORepeatOnTime                      50      // 14 Bits, Bit 13-0
#define     LOG_fORepeatOnTimeMask 0x3FFF
#define     LOG_fORepeatOnTimeShift 0
#define LOG_fORepeatOffBase                     52      // 2 Bits, Bit 7-6
#define     LOG_fORepeatOffBaseMask 0xC0
#define     LOG_fORepeatOffBaseShift 6
#define LOG_fORepeatOffTime                     52      // 14 Bits, Bit 13-0
#define     LOG_fORepeatOffTimeMask 0x3FFF
#define     LOG_fORepeatOffTimeShift 0
#define LOG_fODelay                             54      // 1 Bit, Bit 7
#define     LOG_fODelayMask 0x80
#define     LOG_fODelayShift 7
#define LOG_fODelayOnRepeat                     54      // 2 Bits, Bit 6-5
#define     LOG_fODelayOnRepeatMask 0x60
#define     LOG_fODelayOnRepeatShift 5
#define LOG_fODelayOnReset                      54      // 1 Bit, Bit 4
#define     LOG_fODelayOnResetMask 0x10
#define     LOG_fODelayOnResetShift 4
#define LOG_fODelayOffRepeat                    54      // 2 Bits, Bit 3-2
#define     LOG_fODelayOffRepeatMask 0x0C
#define     LOG_fODelayOffRepeatShift 2
#define LOG_fODelayOffReset                     54      // 1 Bit, Bit 1
#define     LOG_fODelayOffResetMask 0x02
#define     LOG_fODelayOffResetShift 1
#define LOG_fOStair                             54      // 1 Bit, Bit 0
#define     LOG_fOStairMask 0x01
#define     LOG_fOStairShift 0
#define LOG_fORetrigger                         55      // 1 Bit, Bit 7
#define     LOG_fORetriggerMask 0x80
#define     LOG_fORetriggerShift 7
#define LOG_fOStairOff                          55      // 1 Bit, Bit 6
#define     LOG_fOStairOffMask 0x40
#define     LOG_fOStairOffShift 6
#define LOG_fORepeat                            55      // 1 Bit, Bit 5
#define     LOG_fORepeatMask 0x20
#define     LOG_fORepeatShift 5
#define LOG_fOOutputFilter                      55      // 2 Bits, Bit 4-3
#define     LOG_fOOutputFilterMask 0x18
#define     LOG_fOOutputFilterShift 3
#define LOG_fOSendOnChange                      55      // 1 Bit, Bit 2
#define     LOG_fOSendOnChangeMask 0x04
#define     LOG_fOSendOnChangeShift 2
#define LOG_fODpt                               56      // 8 Bits, Bit 7-0
#define LOG_fOOnAll                             57      // 8 Bits, Bit 7-0
#define LOG_fOOnDpt1                            58      // 8 Bits, Bit 7-0
#define LOG_fOOnDpt2                            58      // 8 Bits, Bit 7-0
#define LOG_fOOnDpt3Dir                         58      // 5 Bits, Bit 7-3
#define     LOG_fOOnDpt3DirMask 0xF8
#define     LOG_fOOnDpt3DirShift 3
#define LOG_fOOnDpt3Dim                         58      // 3 Bits, Bit 2-0
#define     LOG_fOOnDpt3DimMask 0x07
#define     LOG_fOOnDpt3DimShift 0
#define LOG_fOOnDpt5                            58      // uint8_t
#define LOG_fOOnDpt5001                         58      // uint8_t
#define LOG_fOOnDpt6                            58      // int8_t
#define LOG_fOOnDpt7                            58      // uint16_t
#define LOG_fOOnDpt8                            58      // int16_t
#define LOG_fOOnDpt9                            58      // float (4 Byte)
#define LOG_fOOnDpt12                           58      // uint32_t
#define LOG_fOOnDpt13                           58      // int32_t
#define LOG_fOOnDpt14                           58      // float (4 Byte)
#define LOG_fOOnDpt16                           58      // char*, 14 Byte
#define     LOG_fOOnDpt16Length 14
#define LOG_fOOnDpt17                           58      // 8 Bits, Bit 7-0
#define LOG_fOOnRGB                             58      // 24 Bits, Bit 31-8
#define     LOG_fOOnRGBMask 0xFFFFFF00
#define     LOG_fOOnRGBShift 8
#define LOG_fOOnLedProvider                     62      // 3 Bits, Bit 2-0
#define     LOG_fOOnLedProviderMask 0x07
#define     LOG_fOOnLedProviderShift 0
#define LOG_fOOnLedEffect                       63      // 3 Bits, Bit 2-0
#define     LOG_fOOnLedEffectMask 0x07
#define     LOG_fOOnLedEffectShift 0
#define LOG_fOOnLedDuration                     64      // uint16_t
#define LOG_fOOnPAArea                          58      // 4 Bits, Bit 7-4
#define     LOG_fOOnPAAreaMask 0xF0
#define     LOG_fOOnPAAreaShift 4
#define LOG_fOOnPALine                          58      // 4 Bits, Bit 3-0
#define     LOG_fOOnPALineMask 0x0F
#define     LOG_fOOnPALineShift 0
#define LOG_fOOnPADevice                        59      // uint8_t
#define LOG_fOOnFunction                        58      // 8 Bits, Bit 7-0
#define LOG_fOOnKOKind                          63      // 2 Bits, Bit 7-6
#define     LOG_fOOnKOKindMask 0xC0
#define     LOG_fOOnKOKindShift 6
#define LOG_fOOnKONumber                        58      // uint16_t
#define LOG_fOOnKONumberRel                     58      // int16_t
#define LOG_fOOnKODpt                           60      // 8 Bits, Bit 7-0
#define LOG_fOOnKOSend                          63      // 2 Bits, Bit 5-4
#define     LOG_fOOnKOSendMask 0x30
#define     LOG_fOOnKOSendShift 4
#define LOG_fOOnKOSendNumber                    64      // uint16_t
#define LOG_fOOnKOSendNumberRel                 64      // int16_t
#define LOG_fOOffAll                            72      // 8 Bits, Bit 7-0
#define LOG_fOOffDpt1                           73      // 8 Bits, Bit 7-0
#define LOG_fOOffDpt2                           73      // 8 Bits, Bit 7-0
#define LOG_fOOffDpt3Dir                        73      // 5 Bits, Bit 7-3
#define     LOG_fOOffDpt3DirMask 0xF8
#define     LOG_fOOffDpt3DirShift 3
#define LOG_fOOffDpt3Dim                        73      // 3 Bits, Bit 2-0
#define     LOG_fOOffDpt3DimMask 0x07
#define     LOG_fOOffDpt3DimShift 0
#define LOG_fOOffDpt5                           73      // uint8_t
#define LOG_fOOffDpt5001                        73      // uint8_t
#define LOG_fOOffDpt6                           73      // int8_t
#define LOG_fOOffDpt7                           73      // uint16_t
#define LOG_fOOffDpt8                           73      // int16_t
#define LOG_fOOffDpt9                           73      // float (4 Byte)
#define LOG_fOOffDpt12                          73      // uint32_t
#define LOG_fOOffDpt13                          73      // int32_t
#define LOG_fOOffDpt14                          73      // float (4 Byte)
#define LOG_fOOffDpt16                          73      // char*, 14 Byte
#define     LOG_fOOffDpt16Length 14
#define LOG_fOOffDpt17                          73      // 8 Bits, Bit 7-0
#define LOG_fOOffRGB                            73      // 24 Bits, Bit 31-8
#define     LOG_fOOffRGBMask 0xFFFFFF00
#define     LOG_fOOffRGBShift 8
#define LOG_fOOffLedProvider                    77      // 3 Bits, Bit 2-0
#define     LOG_fOOffLedProviderMask 0x07
#define     LOG_fOOffLedProviderShift 0
#define LOG_fOOffLedEffect                      78      // 3 Bits, Bit 2-0
#define     LOG_fOOffLedEffectMask 0x07
#define     LOG_fOOffLedEffectShift 0
#define LOG_fOOffLedDuration                    79      // uint16_t
#define LOG_fOOffPAArea                         73      // 4 Bits, Bit 7-4
#define     LOG_fOOffPAAreaMask 0xF0
#define     LOG_fOOffPAAreaShift 4
#define LOG_fOOffPALine                         73      // 4 Bits, Bit 3-0
#define     LOG_fOOffPALineMask 0x0F
#define     LOG_fOOffPALineShift 0
#define LOG_fOOffPADevice                       74      // uint8_t
#define LOG_fOOffFunction                       73      // 8 Bits, Bit 7-0
#define LOG_fOOffKOKind                         78      // 2 Bits, Bit 7-6
#define     LOG_fOOffKOKindMask 0xC0
#define     LOG_fOOffKOKindShift 6
#define LOG_fOOffKONumber                       73      // uint16_t
#define LOG_fOOffKONumberRel                    73      // int16_t
#define LOG_fOOffKODpt                          75      // 8 Bits, Bit 7-0
#define LOG_fOOffKOSend                         78      // 2 Bits, Bit 5-4
#define     LOG_fOOffKOSendMask 0x30
#define     LOG_fOOffKOSendShift 4
#define LOG_fOOffKOSendNumber                   79      // uint16_t
#define LOG_fOOffKOSendNumberRel                79      // int16_t
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
